AntonisPsarras/guardian-system/scripts.yaml

guardian_set_display:
  alias: Guardian - Set Portal Display
  description: >-
    The single way to put a verdict on the portal. Writes the state string and
    then bumps input_number.portal_display_seq.

    The bump is the whole point. input_text.set_value writing a value the helper
    ALREADY holds emits no state_changed event, and two consumers depended on
    that event: "Guardian: Portal LED Mirror", whose GRANTED branch sleeps three
    seconds and then writes IDLE, and the portal's own repaint/backlight wake,
    which tested "st != ui_prev_state".

    So a second identical verdict arriving inside the first one's three-second
    window was swallowed entirely - the screen never acknowledged it, and the
    FIRST run's delay still dropped the screen to IDLE underneath it. Scanning a
    card immediately after enrolling it is exactly that sequence (enrollment
    writes GRANTED, the scan writes GRANTED again), which is why a freshly
    enrolled card appeared to be ignored while its welcome tone and green lamp
    still fired. Unknown cards write a DIFFERENT value, DENIED_CARD, so they
    always changed state and always rendered - the asymmetry that made this look
    like a card-matching bug.

    A counter that always changes makes every verdict observable, repeat or not.
  # queued: this is a read-modify-write on the counter and several automations
  # can call it at once. Queued runs execute sequentially, and action data
  # templates render per-run at execution time, so the increment cannot lose a
  # write the way an automation-level variable would.
  #
  # max is 25 rather than 10 because ONE caller must never be dropped. A
  # blocking "action: script.guardian_set_display" against a queued script that
  # is already at max is DISCARDED with a log warning - it does not raise, and
  # the caller carries on as if it had run. In "Guardian: Major Alarm Handler"
  # that call is the one deliberately unguarded step, on the reasoning that a
  # failure there means the siren cannot run anyway; the siren loop's
  # while-condition reads the state this script writes. So a dropped run there
  # is an alarm that pushes, returns cleanly, and produces NO siren, NO ALARM
  # screen and no error anywhere - the queue depth is the only thing standing
  # between that and a burst of display writes from a keypad, an enrollment and
  # a scan arriving together. Runs are two helper writes and finish in
  # milliseconds; the depth costs nothing and is not a substitute for keeping
  # this script cheap.
  mode: queued
  max: 25
  fields:
    value:
      description: Display state string, e.g. GRANTED, DENIED_CARD, CHALLENGE, IDLE
      required: true
  sequence:
  - action: input_text.set_value
    target:
      entity_id: input_text.portal_display_state
    data:
      value: '{{ value }}'
  # THE ALARM'S ONLY MEMORY ACROSS A RESTART, and it is written here rather than
  # at any of the fifty-odd call sites deliberately.
  #
  # portal_display_state is declared initial: none, which Home Assistant applies
  # on every start and which skips restore_state - so the display cannot carry an
  # alarm across a restart, and "Guardian: Startup State Recovery" spent its whole
  # life testing it for ALARM in a branch that could never be true. A restart
  # ended a live alarm in total silence: no siren, no second push, and the code
  # written to resume it was unreachable.
  #
  # This script's own alias is "the single way to put a verdict on the portal",
  # and that is exactly the property the latch needs. Setting it here means the
  # latch and the screen move together or not at all - every existing writer,
  # including "Guardian: Dismiss Alarm from Phone" and guardian_reset, clears the
  # latch correctly with no edit, and a future one cannot forget to. Writing it
  # from the call sites instead would be fifty chances to disagree with the
  # screen about whether the house is alarming.
  #
  # GUARDED, AND IT MATTERS WHICH SIDE OF THE DISPLAY WRITE IT SITS ON.
  #
  # The write above is the one deliberately unguarded step in the alarm path,
  # because the siren loop's while-condition reads what it writes: if that fails
  # the siren genuinely cannot run and the error belongs in the log. THIS step
  # does not have that property. Failing to record the latch means an alarm will
  # not survive a restart, which is strictly less bad than an alarm that never
  # sounds - so it must not be able to take the sounding one with it.
  #
  # And it would have been able to. guardian_set_display is called BLOCKING from
  # "Guardian: Major Alarm Handler", so a step that ends this script ends the
  # handler too - in front of its own siren loop. That is the exact fault the
  # fortieth and forty-second passes each fixed once: a cosmetic step standing in
  # front of the siren, with a comment above it explaining why it was safe. On a
  # half-installed tree - packages/guardian.yaml not copied, or copied and only
  # reloaded rather than fully restarted - this helper does not exist, and that
  # is precisely the case the alarm path has already been found failing in.
  #
  # The entity_id is a literal constant, so it cannot fail the service schema and
  # the one failure mode left is a missing or unavailable entity, which is what
  # continue_on_error genuinely does catch.
  - action: input_text.set_value
    continue_on_error: true
    target:
      entity_id: input_text.guardian_alarm_latch
    data:
      # A timestamp, not a flag: the startup reader needs to know HOW LONG AGO,
      # because a restore snapshot can be fifteen minutes stale and an alarm that
      # started eight hours ago is a power cut, not an intrusion.
      value: "{{ now().isoformat() if value == 'ALARM' else 'none' }}"
  - action: input_number.set_value
    target:
      entity_id: input_number.portal_display_seq
    data:
      value: "{{ (states('input_number.portal_display_seq') | int(0) + 1) % 10000 }}"

process_rfid_scan:
  alias: Guardian - Process RFID Scan
  description: >-
    Validates one scan and starts an entry, exit, or MFA passage window.

    NOTHING in here may block. Every lamp call is fired with script.turn_on
    rather than "action: script.guardian_lamp_*", because "action:" WAITS for the
    called script to finish and guardian_lamp_feedback takes 2-3 seconds on a
    good day: a 15s wait_template on the sampling flag, a light.turn_on against a
    cloud-connected Tapo bulb, a 1s hold, then a restore.

    That is how this script silently stopped seeing cards. It is queued with
    max: 10, so ten runs each parked on the lamp fill the queue and Home
    Assistant DROPS every further scan with only a warning in the log - no
    screen change, no audio, nothing on the ESP. It went unnoticed while
    enrollment disabled itself after a single card; now that a session stays
    open and cards are presented one after another, the queue fills in seconds
    and the reader appears to go dead.

    The remaining "action: script.*" calls are guardian_set_display,
    guardian_reconcile_presence, guardian_authorize_passage and
    guardian_clear_entry_challenge. All of them are helper writes and events;
    none wait on the lamp or a delay. They stay as "action:" because the
    branch after them depends on their result. Do not convert them to
    script.turn_on, and do not put a delay or a lamp wait back in this script.
  mode: queued
  max: 10
  fields:
    uid:
      description: Legacy factory UID from pre-authenticator firmware. Ignored when result is set.
      required: false
    source:
      description: doorbell or interior_portal
      required: true
    result:
      description: ok, enrolled, write_fail, bad_mac, or unsupported_tag
      required: false
    card_id:
      description: 16-character hex card_id from the on-card authenticator
      required: false
    counter:
      description: Counter reported by the reader (post-rotate when rotated is true)
      required: false
    rotated:
      description: true if the reader wrote the next counter to the card
      required: false
    protected:
      description: >-
        "true" or "false" from the reader: whether this tag's payload is
        password-protected on the card. EMPTY MEANS UNKNOWN, not false - a
        reader running firmware older than the forty-third pass does not send
        this field at all, and every device in this house is currently running
        such a build. Recorded only; it gates nothing.
      required: false
  sequence:
  - variables:
      scan_result: '{{ result | default('''', true) | string | trim | lower }}'
      card_id_norm: '{{ card_id | default('''', true) | string | trim | lower }}'
      counter_n: '{{ counter | default(0, true) | int(0) }}'
      rotated_b: '{{ (rotated | default(false, true) | string | lower) in [''true'', ''on'', ''1''] }}'
      uid_raw: '{{ uid | default('''', true) | string | trim }}'
      uid_hash: '{{ uid | default('''', true) | string | trim | sha256 if (uid | default('''', true) | string | trim | length) > 0 else '''' }}'
      slot_ids: "{{ (states('sensor.guardian_rfid_slots') | string).split(',')
                   | map('trim') | reject('eq', '') | list }}"
      # Occupied = 16 hex card_id. A leftover rfid_N_hash is not a credential.
      matched_slot: >-
        {% set ids = (states('sensor.guardian_rfid_slots') | string).split(',')
                     | map('trim') | reject('eq', '') | list %}
        {% set cid = card_id | default('', true) | string | trim | lower %}
        {% set ns = namespace(slot='') %}
        {% if cid | length == 16 and cid is match('^[0-9a-f]{16}$') %}
          {% for i in ids %}
            {% set stored = states('input_text.rfid_' ~ i ~ '_card_id')
                            | string | trim | lower %}
            {% if stored | length == 16 and stored is match('^[0-9a-f]{16}$')
                 and stored == cid %}
              {% set ns.slot = i | string %}
            {% endif %}
          {% endfor %}
        {% elif (result | default('', true) | string | trim | length) == 0 %}
          {# Pre-flash firmware still sends uid and no result. Match the old
             hash for the one-restart overlap, then it dies: enrollment no
             longer writes hashes, and flashed readers always send result. #}
          {% set uh = uid | default('', true) | string | trim | sha256 %}
          {% for i in ids %}
            {% set stored = states('input_text.rfid_' ~ i ~ '_hash')
                            | string | trim | lower %}
            {% if stored | length == 64 and stored == uh %}
              {% set ns.slot = i | string %}
            {% endif %}
          {% endfor %}
        {% endif %}
        {{ ns.slot }}
      empty_slot: >-
        {% set ids = (states('sensor.guardian_rfid_slots') | string).split(',')
                     | map('trim') | reject('eq', '') | list %}
        {% set ns = namespace(slot='') %}
        {% for i in ids %}
          {% set value = states('input_text.rfid_' ~ i ~ '_card_id')
                         | string | trim | lower %}
          {% if ns.slot == '' and not (value | length == 16
               and value is match('^[0-9a-f]{16}$')) %}
            {% set ns.slot = i | string %}
          {% endif %}
        {% endfor %}
        {{ ns.slot }}
      # Single source of truth - see binary_sensor.guardian_elevated_mode in
      # packages/guardian.yaml. This used to read
      # "super_surveillance_mode == on or now().hour < 5" inline, one of four
      # copies, which meant the clock half could not be switched off and no
      # automation anywhere could react to elevated mode ending. Elevated is
      # now the manual boolean OR the Super Surveillance schedule.
      elevated_mode: "{{ is_state('binary_sensor.guardian_elevated_mode', 'on') }}"
      enroll_mode: "{{ is_state('input_boolean.guardian_enrollment_mode', 'on') }}"
      enroll_as_visitor: "{{ is_state('input_boolean.guardian_enroll_as_visitor', 'on') }}"
      # A grace challenge is open: the door was opened in elevated mode without a
      # completed passage window, and someone has a few seconds to present BOTH
      # a registered card and the master PIN. One factor is not enough.
      challenge_active: "{{ is_state('input_boolean.guardian_entry_challenge', 'on') }}"
      # Which slot an enrollment writes to. The keypad choice wins; otherwise the
      # first free slot; empty when every slot is occupied and nothing was
      # chosen, which is now an explicit "pick a slot" prompt on the portal
      # rather than a silent refusal.
      #
      # sensor.guardian_enrollment_target_slot computes exactly this and is what
      # the portal renders, but it is deliberately NOT read here: a template
      # sensor is recomputed from a state change, and enrolling two cards back to
      # back would race it - the second card could be written into the slot the
      # first one just took. This is derived from the helpers directly so the
      # write is always against current truth.
      target_slot: >-
        {%- set ids = (states('sensor.guardian_rfid_slots') | string).split(',')
                      | map('trim') | reject('eq', '') | list -%}
        {%- set chosen = states('input_text.guardian_enrollment_slot')
                         | string | trim -%}
        {{- chosen if chosen in ids else (empty_slot | string | trim) -}}
      # Home Assistant coerces a script variable whose rendered value is only
      # digits into an int. empty_slot / target_slot / matched_slot therefore
      # arrive at the choose as 1, not "1". Jinja's `1 in ['1','2']` is
      # false, so enrollment with empty hashes took ENROLL_PICK ("no
      # target slot") while the trace printed target_slot: '1'. Every
      # comparison below must `| string | trim` before testing membership.
      slot_ok: "{{ (matched_slot | string | trim) in ((states('sensor.guardian_rfid_slots')
        | string).split(',') | map('trim') | reject('eq', '') | list) }}"
      target_ok: "{{ (target_slot | string | trim) in ((states('sensor.guardian_rfid_slots')
        | string).split(',') | map('trim') | reject('eq', '') | list) }}"
      # Freshness window against the last counter Home Assistant stored.
      # seen is the counter that was on the card BEFORE a successful rotate.
      # Accept stored-1 (last write did not stick) and anything newer (HA missed
      # a rotate, or the other reader already wrote). Older than stored-1 is a
      # dump clone. The old stored+1 cap treated a double-scan the reader
      # ingested once as CLONE; that high cap is not clone detection.
      #
      # The `not (rot and reported <= stored)` clause is REPLAY protection, and
      # it is deliberately narrow. esphome.rfid_scanned is an ordinary event on
      # the bus: any account that can authenticate to Home Assistant can POST one
      # to /api/events/esphome.rfid_scanned, and the two values needed to build a
      # convincing payload - input_text.rfid_N_card_id and
      # input_number.rfid_N_counter - are readable from the states API. The
      # firmware's HMAC is not checked here; only this window is.
      #
      # Work out which case actually changes. For a rotated scan the old rule
      # reduces to `stored <= reported` (substitute seen = reported - 1). The new
      # clause requires `stored < reported`. So the ONLY behaviour that changes is
      # rotated scans where reported == stored exactly - a card claiming to have
      # just rotated INTO a value Home Assistant has already recorded. A genuine
      # tap can never do that: the write-back below stores `reported`, so the next
      # genuine tap of the same card reports stored + 1. Replaying a captured
      # event verbatim is precisely the case that produces reported == stored.
      #
      # Non-rotated scans (rot false, the card write failed) are untouched, and
      # so is the stale-dump case, which the lower bound already caught.
      #
      # The cost of a false positive here is not small - this branch produces the
      # CLONE verdict, a critical push, and a major alarm if a challenge is open -
      # so if a real double-tap ever reports CLONE, this clause is the first thing
      # to look at, not the branch ordering further down.
      window_ok: >-
        {% set slot = matched_slot | string | trim %}
        {% set ids = (states('sensor.guardian_rfid_slots') | string).split(',')
                     | map('trim') | reject('eq', '') | list %}
        {% if slot not in ids %}
          {{ false }}
        {% else %}
          {% set stored = states('input_number.rfid_' ~ slot ~ '_counter') | int(0) %}
          {% set reported = counter | default(0, true) | int(0) %}
          {% set rot = (rotated | default(false, true) | string | lower)
                       in ['true', 'on', '1'] %}
          {% set seen = reported - (1 if rot and reported > 0 else 0) %}
          {{ (stored - 1 <= seen) and not (rot and reported <= stored) }}
        {% endif %}
      tag_unsupported: "{{ scan_result == 'unsupported_tag' }}"
      enroll_hold: "{{ scan_result in ['write_fail', 'bad_mac'] }}"
      # THREE-VALUED ON PURPOSE: 'true', 'false', or '' for not-stated. Anything
      # the reader did not send stays '' and is recorded as nothing at all,
      # because a firmware that predates this field is indistinguishable from one
      # reporting an unprotected tag if the two are collapsed - and the whole
      # point of surfacing this is to tell a household which of their keys are
      # clonable. Reading silence as "unprotected" would accuse every key in the
      # house; reading it as "protected" would clear them all. It reads as
      # neither.
      protected_norm: >-
        {% set p = protected | default('', true) | string | trim | lower %}
        {{ 'true' if p in ['true', 'on', '1', 'yes']
           else ('false' if p in ['false', 'off', '0', 'no'] else '') }}
  # A key flagged Stolen/Lost, presented at EITHER reader, sounds the alarm here
  # and now - before the decision trace, before reconcile, before the counter
  # write, before the choose. Both readers reach this line: the doorbell and the
  # portal both dispatch through "Guardian: RFID Scanned" into this one script,
  # and both are heard on the portal's DFPlayer, which is where every other
  # scan sound already comes from.
  #
  # The assumption is that the person holding a key its owner reported missing
  # is an intruder standing at the door right now, so this must not wait on
  # anything that can be slow or absent. It reads two local helpers and presses
  # one ESPHome button on the LAN: no phone link, no cloud bulb, no broadcast.
  # This press, and ONLY this press, is what has to happen with no latency. It
  # is not routed through guardian.major_alarm because that handler writes the
  # reason, sets the display and fires notify_broadcast before it reaches its
  # play loop. The alarm proper is raised a few lines below, once matched_name
  # exists; that is what sustains the siren, lights the screen and offers the
  # phone its Disable Alarm button. This is just the first note of it, early.
  #
  # Nothing above it may suppress it either. There is no cooldown or
  # "already alarming" test here on purpose: a second stolen tap means someone
  # is still at the door, and a silent second tap is the failure this exists to
  # prevent.
  #
  # continue_on_error, and it is the whole difference between an early note and
  # a silent alarm. The press targets an entity on the PORTAL; the scan can come
  # from the DOORBELL, which does not need the portal to be up. With the portal
  # unavailable - rebooting, roaming between access points, the five minutes
  # "Guardian: Portal Offline Watchdog" exists to announce - button.press raises,
  # and a raising step ends the sequence. Unguarded, this line took the whole
  # script down with it: guardian.major_alarm below never fired, so there was no
  # push, no reason written, no ALARM display and no siren loop to resume when
  # the portal came back, and the rest of process_rfid_scan - trace, reconcile,
  # counter write, the entire choose - never ran either. A stolen key at the
  # door produced silence.
  #
  # This is the same class of fault the Major Alarm Handler was fixed for in
  # 8e89db4, on a worse path: it needs no half-copied install and no startup
  # race, only a portal that is briefly off the network. The guard costs
  # nothing - continue_on_error adds no latency and does not defer the press,
  # it only stops a failed press from suppressing everything after it. If the
  # speaker cannot sound, the alarm proper below still must.
  - if:
    - condition: template
      value_template: "{{ slot_ok | bool and
        states('input_select.rfid_' ~ (matched_slot | string | trim))
          in ['Stolen', 'Stolen/Lost'] }}"
    then:
    - action: button.press
      continue_on_error: true
      target:
        entity_id: button.guardian_interior_portal_play_alarm
  - variables:
      # Person name for user-facing copy. Recomputed here so it can read
      # matched_slot from the previous variables block (same-block keys cannot
      # reference each other).
      matched_name: >-
        {% set i = matched_slot | string | trim %}
        {% set raw = states('input_text.rfid_' ~ i ~ '_name') | string | trim %}
        {{ raw if raw not in ['', 'unknown', 'unavailable']
           else ('Key ' ~ i if i else '') }}
      # Presence BEFORE reconcile. A doorbell scan of an "At home" card is an
      # exit that already left the house; reconcile would flip it to Away and
      # hide that from every later branch. Capture it here, then never read
      # input_select.rfid_N again for this decision.
      presence_before: >-
        {% set i = matched_slot | string | trim %}
        {{ states('input_select.rfid_' ~ i) | string | trim }}
      door_closed: "{{ is_state('binary_sensor.guardian_interior_portal_door_contact', 'off') }}"
      # Exterior reader, door shut, elevated: the keypad is unreachable. Either
      # a live 30s challenge (they just walked out) or presence still At home
      # (they left without scanning inside) is an exit that needs the 10-minute
      # phone PIN, not MFA at a keypad they cannot reach.
      doorbell_exit: "{{ (elevated_mode | bool) and (source == 'doorbell')
        and (door_closed | bool) and (slot_ok | bool)
        and ((challenge_active | bool) or (presence_before == 'At home')) }}"
  # Raise the alarm proper for a Stolen/Lost key, still ahead of the trace,
  # reconcile, the counter write and the choose. The siren already started
  # above; this is what keeps it going and makes it stoppable.
  #
  # Everything the previous version of this had to invent, the major alarm
  # already owns, which is why it is now raised unconditionally here rather
  # than only when a challenge happened to be live:
  #
  #   * the siren repeats on a 3s cadence for as long as the display says
  #     ALARM, instead of a fixed count that ran out while the intruder was
  #     still at the door;
  #   * "Guardian: Dismiss Alarm from Phone" answers MUTE_GUARDIAN_ALARM by
  #     writing IDLE, which is what ends that loop - the phone button the
  #     super surveillance alarm already offers now stops this one too;
  #   * the portal paints its full-screen ALARM with the reason below. The
  #     STOLEN screen could not be used for this: "Guardian: Portal LED Mirror"
  #     drops STOLEN back to IDLE after three seconds, so the screen went blank
  #     while the siren kept sounding.
  #
  # The reason is rendered at 35 characters on a 240px panel, so it leads with
  # the two words that matter and abbreviates the reader rather than letting a
  # long name push them off the end.
  - if:
    - condition: template
      value_template: "{{ slot_ok | bool and
        states('input_select.rfid_' ~ (matched_slot | string | trim))
          in ['Stolen', 'Stolen/Lost'] }}"
    then:
    - event: guardian.major_alarm
      event_data:
        reason: >-
          Stolen key: {{ matched_name if matched_name else 'Key ' ~
          (matched_slot | string | trim) }} at {{ 'door' if source == 'doorbell'
          else 'portal' }}
  # Decision trace. OFF unless input_boolean.guardian_verbose_notifications is on.
  #
  # This lives HERE, inside the script, rather than in an automation watching the
  # event, because it has to report the variables the choose below will actually
  # branch on. Every other vantage point - the device log, the event bus, a
  # template sensor - shows an input to this decision rather than the decision,
  # and the failures being chased have all been cases where the inputs looked
  # right and the outcome was still wrong.
  #
  # It names the branch outright, computed from the same conditions in the same
  # order, so "which branch ran" stops being an inference from an LED colour.
  - if:
    - condition: state
      entity_id: input_boolean.guardian_verbose_notifications
      state: 'on'
    then:
    # continue_on_error: this is a diagnostic, and it sits in front of every
    # alert the scan can raise - the stolen-key alarm, the clone push and the
    # clone alarm all come after it. A trace that can cancel the thing it exists
    # to explain is worse than no trace.
    - action: persistent_notification.create
      continue_on_error: true
      data:
        notification_id: "guardian_scan_trace_{{ now().strftime('%H%M%S') }}"
        title: >-
          {{ now().strftime('%H:%M:%S') }} {{ source }} ->
          {%- set m = matched_slot | string | trim -%}
          {%- set valid = slot_ok | bool -%}
          {% if valid and states('input_select.rfid_' ~ m)
                in ['Stolen', 'Stolen/Lost'] %} STOLEN
          {%- elif doorbell_exit | bool %} DOORBELL EXIT PIN
          {%- elif challenge_active | bool and valid %} CHALLENGE CARD
          {%- elif enroll_mode | bool and valid %} ENROLL_DUP
          {%- elif valid and not (window_ok | bool) and scan_result not in ['', 'enrolled'] %} CLONE
          {%- elif enroll_hold | bool %} HOLD
          {%- elif valid and elevated_mode | bool %} MFA
          {%- elif valid %} GRANTED (passage)
          {%- elif enroll_mode | bool and tag_unsupported | bool %} UNSUPPORTED
          {%- elif enroll_mode | bool and enroll_hold | bool %} HOLD
          {%- elif enroll_mode | bool and target_ok | bool %} ENROLL -> slot {{ target_slot | string | trim }}
          {%- elif enroll_mode | bool %} ENROLL_PICK (no target slot)
          {%- elif tag_unsupported | bool %} UNSUPPORTED
          {%- else %} DENIED_CARD{% endif %}
        message: >-
          result: {{ scan_result }}
          · card_id_len: {{ card_id_norm | length }}
          · counter: {{ counter_n }}
          · rotated: {{ rotated_b }}
          · window: {{ window_ok }}

          matched_slot: '{{ matched_slot | string | trim }}'
          · empty_slot: '{{ empty_slot | trim }}'
          · target_slot: '{{ target_slot | string | trim }}'

          enroll_mode: {{ enroll_mode }}
          · guest: {{ enroll_as_visitor }}
          · elevated: {{ elevated_mode }}
          · challenge: {{ challenge_active }}
          · doorbell_exit: {{ doorbell_exit }}
          · presence_before: '{{ presence_before }}'

          enrollment_slot helper: '{{ states('input_text.guardian_enrollment_slot') }}'

          stored: {% set ids = (states('sensor.guardian_rfid_slots') | string).split(',')
                               | map('trim') | reject('eq', '') | list %}{% for i in ids %}{{ i }}={{
            states('input_text.rfid_' ~ i ~ '_card_id') | string | trim | lower | length }}ch/c{{
            states('input_number.rfid_' ~ i ~ '_counter') | int(0) }} {% endfor %}
  # Self-correction, before any branch. The reader a card was presented to tells
  # us which side of the door that card is physically on, so a card recorded as
  # "Away" and scanned on the interior portal - or "At home" and scanned at the
  # doorbell - is provably out of date from an earlier missed scan. Fix it now
  # rather than letting the error persist.
  #
  # Placed ahead of the choose so it covers the normal path AND the elevated
  # MFA path from one call site. Stolen cards are excluded: their branch is a
  # security response, and their input_select state must not be touched.
  - if:
    - condition: template
      value_template: "{{ slot_ok | bool and
        (scan_result == '' or window_ok | bool) and
        states('input_select.rfid_' ~ (matched_slot | string | trim))
          not in ['Stolen', 'Stolen/Lost'] }}"
    then:
    - action: script.guardian_reconcile_presence
      data:
        slot: '{{ matched_slot | string | trim }}'
        source: '{{ source }}'
  # Record the new counter only after the window accepted it, and only when the
  # reader actually wrote. A failed rotate leaves HA where it was so the next
  # tap still matches. A clone (window fail) must not advance this.
  - if:
    - condition: template
      value_template: "{{ slot_ok | bool and rotated_b | bool and
        (scan_result == '' or window_ok | bool) }}"
    then:
    - action: input_number.set_value
      continue_on_error: true
      target:
        entity_id: input_number.rfid_{{ matched_slot | string | trim }}_counter
      data:
        value: "{{ [states('input_number.rfid_' ~ (matched_slot | string | trim) ~ '_counter')
          | int(0), counter_n | int(0)] | max }}"
  # Read back before any grant. continue_on_error above means a missing helper
  # cannot abort the stolen-key path that already ran, but it also used to
  # swallow a persist that never landed - then GRANTED still fired, and the
  # next tap looked like a replay. Fail closed: if this rotate did not stick
  # on the helper, no passage window.
  - variables:
      counter_ok: "{{ (not (slot_ok | bool) or not (rotated_b | bool)) or
        (states('input_number.rfid_' ~ (matched_slot | string | trim) ~ '_counter')
         | int(0) >= (counter_n | int(0))) }}"
  # WHETHER THIS KEY IS PASSWORD-PROTECTED ON THE CARD. Recorded here, shown in
  # the panel's key list, and USED FOR NOTHING ELSE.
  #
  # The reader has published this on every scan since the forty-third pass and
  # nothing has ever read it - the field went onto the event bus and stopped
  # there, while DEPLOY.md recorded it as "surfaced to the household". An
  # unprotected NTAG's payload can be read by any reader, and a readable bearer
  # token is a clonable card, so the household has a reason to know which of
  # their keys are in that state.
  #
  # IT MUST NEVER GATE ACCESS, and that is not caution, it is the two lessons
  # this component has already paid for: refusing an unprotected tag would lock
  # out every card enrolled before the protection fix existed, which is the
  # entire house, and it is the population that most needs to be let in and told.
  # This step writes one CSV helper. It is not read by any condition on any path
  # that opens a door.
  #
  # Only writes on a definite verdict. protected_norm is '' when the reader did
  # not state it, and a slot is then left exactly as it was rather than being
  # cleared - a scan from an old firmware must not erase a finding a new one made.
  - if:
    - condition: template
      value_template: "{{ slot_ok | bool and protected_norm in ['true', 'false'] }}"
    then:
    - action: input_text.set_value
      continue_on_error: true
      target:
        entity_id: input_text.guardian_card_protection
      data:
        # Rebuilt from the current value on every write rather than appended to,
        # so the string cannot accumulate duplicate or stale entries. Entries for
        # slots that no longer exist are dropped, this slot's old entry is
        # replaced by the fresh verdict, and the result is sorted so two
        # identical sets are always the same string - a helper that flickers
        # between equivalent orderings would repaint the panel for no reason.
        value: >-
          {%- set slot = matched_slot | string | trim -%}
          {%- set ids = (states('sensor.guardian_rfid_slots') | string).split(',')
                        | map('trim') | reject('eq', '') | list -%}
          {%- set held = (states('input_text.guardian_card_protection') | string)
                         .split(',') | map('trim') | reject('eq', '') | list -%}
          {%- set ns = namespace(out=[]) -%}
          {%- for e in held -%}
            {%- if e is match('^[0-9]+[pu]$') -%}
              {%- set who = e[:-1] -%}
              {%- if who != slot and who in ids -%}
                {%- set ns.out = ns.out + [e] -%}
              {%- endif -%}
            {%- endif -%}
          {%- endfor -%}
          {%- set ns.out = ns.out
                + [slot ~ ('u' if protected_norm == 'false' else 'p')] -%}
          {{- ns.out | sort | join(',') -}}
  - choose:
    - conditions:
      - condition: template
        value_template: '{{ tag_unsupported | bool }}'
      sequence:
      - event: guardian.unknown_card_scanned
        event_data:
          source: '{{ source }}'
          result: unsupported_tag
      - action: script.guardian_set_display
        data:
          value: UNSUPPORTED
      - action: button.press
        target:
          entity_id: button.guardian_interior_portal_play_denied
      - action: script.turn_on
        target:
          entity_id: script.guardian_lamp_rejected
    - conditions:
      - condition: template
        value_template: '{{ slot_ok | bool and scan_result not in ['''', ''enrolled'']
          and not (window_ok | bool) and states(''input_select.rfid_'' ~
          (matched_slot | string | trim)) not in [''Stolen'', ''Stolen/Lost''] }}'
      sequence:
      - event: guardian.clone_card_scanned
        event_data:
          slot: '{{ matched_slot | string | trim }}'
          name: '{{ matched_name }}'
          source: '{{ source }}'
          counter: '{{ counter_n }}'
      - action: script.guardian_notify_person
        continue_on_error: true
        data:
          slot: '{{ matched_slot | string | trim }}'
          critical: true
          category: security
          severity: urgent
          title: 'Guardian: copied key rejected'
          message: >-
            {{ matched_name if matched_name else 'Key ' ~ (matched_slot | string | trim) }}
            presented a stale counter at the {{ source }} reader. The real key
            still works; this copy does not. Flag Stolen/Lost if the original
            is missing.
      - action: script.guardian_set_display
        data:
          value: CLONE
      # Guarded for the same reason as the stolen-key press above: this targets
      # a PORTAL entity and a clone can be presented at the doorbell, so an
      # offline portal made this raise and end the branch - taking the
      # guardian.major_alarm below with it. guardian_set_display above stays
      # unguarded on the Major Alarm Handler's rule: the display state is what
      # the siren loop repeats on, so a failure there means no siren regardless
      # and the error belongs in the log rather than swallowed.
      - action: button.press
        continue_on_error: true
        target:
          entity_id: button.guardian_interior_portal_play_denied
      - action: script.turn_on
        target:
          entity_id: script.guardian_lamp_rejected
      # Same escalation as the stolen branch below, for the same reason. This
      # branch is evaluated BEFORE the challenge-factor branch and wins, so a
      # forged copy presented to answer a live challenge used to produce CLONE
      # on the display, a critical push and a red flash - and then nothing, until
      # the challenge ran out 30 seconds later and alarmed with the generic "not
      # authenticated" reason. A copy of a card that is still in its owner's
      # pocket is at least as strong an intruder signal as one already reported
      # missing, and the person holding it is standing at the door now. Do not
      # reorder the branches to "fix" this instead - the clone verdict has to win
      # so the display and the counter logic stay correct.
      - if:
        - condition: template
          value_template: '{{ challenge_active | bool }}'
        then:
        - event: guardian.major_alarm
          event_data:
            reason: >-
              Cloned key ({{ (matched_name ~ ', ') if matched_name else '' }}slot
              {{ matched_slot | string | trim }}) presented to answer an
              elevated-mode entry challenge
    - conditions:
      - condition: template
        value_template: '{{ enroll_mode | bool and not (slot_ok | bool)
          and enroll_hold | bool }}'
      sequence:
      - action: script.guardian_set_display
        data:
          value: HOLD
      - action: button.press
        target:
          entity_id: button.guardian_interior_portal_play_denied
      - action: timer.start
        target:
          entity_id: timer.guardian_enrollment_window
    - conditions:
      - condition: template
        value_template: '{{ slot_ok | bool }}'
      - condition: template
        value_template: '{{ states(''input_select.rfid_'' ~ (matched_slot | string | trim))
          in [''Stolen'', ''Stolen/Lost''] }}'
      sequence:
      - event: guardian.stolen_card_scanned
        event_data:
          slot: '{{ matched_slot | string | trim }}'
          name: '{{ matched_name }}'
          source: '{{ source }}'
      # This branch now announces the scan and nothing else. The major alarm
      # raised at the top of the script owns the screen, the lamp and the
      # speaker for the rest of this event, and each of the three things that
      # used to be done here actively fought it:
      #
      #   * set_display STOLEN raced the handler's own write of ALARM. Landing
      #     second, it took the screen off ALARM - which is the exact condition
      #     the siren loop repeats on - and silenced the alarm about a second
      #     after it started.
      #   * play_denied replaced the alarm track on the DFPlayer, which plays
      #     one file at a time, so a stolen key sounded like an unknown one.
      #   * lamp_rejected flashed red three times and ended on light.turn_off,
      #     then hit its own "Alarm owns the lamp" stop before restoring
      #     anything - leaving the bulb DARK for the rest of an alarm the
      #     handler had just pinned solid red.
      #
      # The escalation that used to be conditional on challenge_active is gone
      # for the same reason: the alarm is now raised for every stolen scan,
      # which is what a key its owner reported missing warrants regardless of
      # whether a challenge happened to be open.
    - conditions:
      - condition: template
        value_template: '{{ slot_ok | bool and rotated_b | bool
          and not (counter_ok | bool) }}'
      sequence:
      # The card write was reported, but input_number.rfid_N_counter did not
      # take the new value. Granting here would play welcome and open a
      # passage window while HA still holds the old counter - or, if a later
      # retry then persisted, the next genuine tap would look like a replay.
      - action: persistent_notification.create
        continue_on_error: true
        data:
          notification_id: guardian_rfid_counter_write_failed
          title: 'Guardian: key counter did not save'
          message: >-
            Slot {{ matched_slot | string | trim }} reported counter
            {{ counter_n | int(0) }} from the {{ source }} reader, but
            input_number.rfid_{{ matched_slot | string | trim }}_counter
            still reads
            {{ states('input_number.rfid_' ~ (matched_slot | string | trim)
               ~ '_counter') | int(0) }}. Passage was not granted.
            Re-present the key after the helper is writable. Hold still and
            retry; do not re-enroll unless the same key has been HOLDed three
            times in a row. Re-enrolling mints a new card_id and hides a
            counter that did not stick.
      - action: script.guardian_set_display
        data:
          value: HOLD
      - action: button.press
        continue_on_error: true
        target:
          entity_id: button.guardian_interior_portal_play_denied
    - conditions:
      - condition: template
        value_template: '{{ enroll_hold | bool and slot_ok | bool }}'
      sequence:
      # Matched write_fail / bad_mac used to fall through to authorize_passage
      # and play welcome. Firmware now retries silently while the tag is on
      # the coil and only emits write_fail when it leaves still failing, so
      # this is the terminal outcome: keep the card, do not open a door.
      # Re-enroll is not the first remedy: it mints a new card_id and resets
      # the counter, which masks a torn rotate. Hold and retry; re-enroll only
      # after three HOLDs on this same key.
      - action: persistent_notification.create
        continue_on_error: true
        data:
          notification_id: guardian_rfid_hold_retry
          title: 'Guardian: hold the key and retry'
          message: >-
            Slot {{ matched_slot | string | trim }} at the {{ source }} reader
            reported {{ scan_result }} (counter
            {{ counter_n | int(0) }}, rotated {{ rotated_b }}). Passage was
            not granted. Keep the key on the reader and tap again. Do not
            re-enroll unless this same key has been HOLDed three times in a
            row — re-enrolling hides a torn write instead of healing it.
      - action: script.guardian_set_display
        data:
          value: HOLD
      - action: button.press
        continue_on_error: true
        target:
          entity_id: button.guardian_interior_portal_play_denied
    # A registered card is one factor of a grace challenge, never both. The
    # previous either/or (card alone cleared it) is the loophole this branch
    # exists to close. Doorbell-exit (door shut, keypad unreachable) is handled
    # above so it is not forced through a 30s keypad wait the owner cannot
    # answer.
    - conditions:
      - condition: template
        value_template: '{{ doorbell_exit | bool }}'
      - condition: template
        value_template: '{{ slot_ok | bool }}'
      sequence:
      - action: script.guardian_start_doorbell_exit_pin
        data:
          slot: '{{ matched_slot | string | trim }}'
          convert_challenge: '{{ challenge_active | bool }}'
    - conditions:
      - condition: template
        value_template: '{{ challenge_active | bool }}'
      - condition: template
        value_template: '{{ slot_ok | bool }}'
      sequence:
      - action: input_boolean.turn_on
        target:
          entity_id: input_boolean.guardian_challenge_card_ok
      - action: input_text.set_value
        target:
          entity_id: input_text.pending_mfa_slot
        data:
          value: '{{ matched_slot | string | trim }}'
      - action: input_text.set_value
        target:
          entity_id: input_text.pending_mfa_source
        data:
          value: '{{ source }}'
      - choose:
        - conditions:
          - condition: state
            entity_id: input_boolean.guardian_challenge_pin_ok
            state: 'on'
          sequence:
          - action: script.guardian_clear_entry_challenge
            data:
              method: card
              slot: '{{ matched_slot | string | trim }}'
              detail: >-
                {{ matched_name if matched_name
                   else 'Key ' ~ (matched_slot | string | trim) }} at {{ source }}
                (PIN already entered)
          - action: script.guardian_set_display
            data:
              value: GRANTED
          - action: button.press
            target:
              entity_id: button.guardian_interior_portal_play_welcome
          - action: script.turn_on
            target:
              entity_id: script.guardian_lamp_success
        default:
        # Card is in; PIN is not. Do not restart the 30s clock (a second scan
        # must not extend the window) and do not GRANTED. The green flash is
        # how the scan is acknowledged while the amber hold stays up.
        - action: script.guardian_set_display
          data:
            value: MFA
        - action: script.turn_on
          target:
            entity_id: script.guardian_lamp_success
        - action: button.press
          target:
            entity_id: button.guardian_interior_portal_play_mfa_challenge
        - action: script.guardian_notify_person
          continue_on_error: true
          data:
            slot: '{{ matched_slot | string | trim }}'
            critical: false
            # The flagship "my key" event, and the single biggest source of the
            # noise this feature exists to cut: one push every time you come
            # home. routine, so it stops at Important - but the mine toggle,
            # which is on by default, deliberately lets it through the level
            # floor anyway. That is what "tell me when my card is scanned"
            # means, and the switch that says so is the way to turn it off.
            category: mine
            severity: routine
            title: 'Guardian: card accepted'
            message: >-
              {{ matched_name if matched_name else ('Key ' ~
              (matched_slot | string | trim)) }} was scanned. Super
              surveillance is still on — enter the master PIN at the keypad.
    # Enrollment mode with a card that is ALREADY registered. Without this the
    # tap fell through to the normal matched branch and silently opened a 20s
    # passage window, so the obvious way to check "did that card actually save?"
    # gave no answer to the question being asked.
    - conditions:
      - condition: template
        value_template: '{{ enroll_mode | bool }}'
      - condition: template
        value_template: '{{ slot_ok | bool }}'
      sequence:
      # Applying the session policy here is how an existing card becomes a
      # visitor (or a resident again) without rewriting its hash: enable
      # enrollment, press 0 for guest, tap the card. Stolen cards never reach
      # this branch.
      - variables:
          dup_slot: '{{ matched_slot | string | trim }}'
          desired_policy: "{{ 'visitor' if enroll_as_visitor | bool else 'resident' }}"
          current_policy: "{{ states('input_select.rfid_' ~ (matched_slot | string | trim)
            ~ '_policy') | string | trim }}"
          policy_options: "{{ state_attr('input_select.rfid_' ~ (matched_slot | string | trim)
            ~ '_policy', 'options') | default([], true) | list }}"
          presence_options: "{{ state_attr('input_select.rfid_' ~ (matched_slot | string | trim),
            'options') | default([], true) | list }}"
          dup_pending_name: "{{ states('input_text.guardian_enroll_pending_name')
            | string | trim }}"
      - if:
        - condition: template
          value_template: "{{ desired_policy != current_policy and
            desired_policy in policy_options }}"
        then:
        - action: input_select.select_option
          continue_on_error: true
          target:
            entity_id: input_select.rfid_{{ dup_slot }}_policy
          data:
            option: '{{ desired_policy }}'
        - if:
          - condition: template
            value_template: "{{ desired_policy == 'visitor' and 'Away' in presence_options }}"
          then:
          - action: input_select.select_option
            continue_on_error: true
            target:
              entity_id: input_select.rfid_{{ dup_slot }}
            data:
              option: Away
      # A typed pending name during this session renames the existing key on
      # re-tap (same helper as a fresh enroll). Empty pending leaves the
      # stored name alone. Pending is cleared only after the name sticks.
      - if:
        - condition: template
          value_template: "{{ dup_pending_name not in ['', 'unknown', 'unavailable', 'none'] }}"
        then:
        - action: input_text.set_value
          continue_on_error: true
          target:
            entity_id: input_text.rfid_{{ dup_slot }}_name
          data:
            value: '{{ dup_pending_name }}'
        - variables:
            dup_name_back: "{{ states('input_text.rfid_' ~ dup_slot ~ '_name')
              | string | trim }}"
        - if:
          - condition: template
            value_template: '{{ dup_name_back == dup_pending_name }}'
          then:
          - action: input_text.set_value
            continue_on_error: true
            target:
              entity_id: input_text.guardian_enroll_pending_name
            data:
              value: ''
      # The slot rides along in the state string. The portal reads it as a
      # prefix match, so "which slot is this card already in" is answerable at
      # the door without adding another imported helper for one digit.
      - action: script.guardian_set_display
        data:
          value: 'ENROLL_DUP:{{ matched_slot | string | trim }}'
      - action: button.press
        target:
          entity_id: button.guardian_interior_portal_play_denied
      # Re-presenting a card is how someone confirms an enrollment worked, so it
      # keeps the session alive rather than letting the idle timer run down
      # underneath them.
      - action: timer.start
        target:
          entity_id: timer.guardian_enrollment_window
    - conditions:
      - condition: template
        value_template: '{{ slot_ok | bool }}'
      - condition: template
        value_template: '{{ elevated_mode | bool }}'
      sequence:
      - action: timer.cancel
        target:
          entity_id:
          - timer.guardian_entry_window
          - timer.guardian_exit_window
      - action: input_text.set_value
        target:
          entity_id:
          - input_text.pending_entry_slot
          - input_text.pending_exit_slot
        data:
          value: none
      - action: timer.cancel
        target:
          entity_id: timer.guardian_mfa_window
      - action: input_text.set_value
        target:
          entity_id: input_text.pending_mfa_slot
        data:
          value: '{{ matched_slot | string | trim }}'
      - action: input_text.set_value
        target:
          entity_id: input_text.pending_mfa_source
        data:
          value: '{{ source }}'
      # A challenge starts with a full three attempts. The portal literally
      # promises this - it renders "3 - mfa_failed_attempts" as "N left" - but
      # the counter was only ever zeroed on a correct PIN, on reaching three,
      # and at Home Assistant start. A challenge that ended by timing out, by
      # being superseded, or by the alarm being dismissed left its count
      # standing, so failures accumulated across unrelated sessions until the
      # very first wrong digit of some later challenge tripped the alarm.
      - action: input_number.set_value
        target:
          entity_id: input_number.mfa_failed_attempts
        data:
          value: 0
      - action: input_boolean.turn_on
        target:
          entity_id: input_boolean.portal_mfa_pending
      - action: timer.start
        target:
          entity_id: timer.guardian_mfa_window
      - action: script.guardian_set_display
        data:
          value: MFA
      - action: script.turn_on
        target:
          entity_id: script.guardian_lamp_success
      - action: button.press
        target:
          entity_id: button.guardian_interior_portal_play_mfa_challenge
      - action: script.guardian_notify_person
        continue_on_error: true
        data:
          slot: '{{ matched_slot | string | trim }}'
          critical: false
          category: mine
          severity: routine
          title: 'Guardian: card accepted'
          message: >-
            {{ matched_name if matched_name else ('Key ' ~
            (matched_slot | string | trim)) }} was scanned. Enter the master
            PIN at the keypad to pass.
    - conditions:
      - condition: template
        value_template: '{{ slot_ok | bool }}'
      - condition: template
        value_template: '{{ counter_ok | bool }}'
      - condition: template
        value_template: '{{ scan_result in ['''', ''ok''] }}'
      sequence:
      - action: script.guardian_authorize_passage
        data:
          slot: '{{ matched_slot | string | trim }}'
          source: '{{ source }}'
    - conditions:
      - condition: template
        value_template: '{{ enroll_mode | bool }}'
      - condition: template
        value_template: '{{ target_ok | bool }}'
      - condition: template
        value_template: '{{ not (card_id_norm | length == 16 and card_id_norm is match(''^[0-9a-f]{16}$'')) }}'
      sequence:
      - action: script.guardian_set_display
        data:
          value: HOLD
      - action: button.press
        target:
          entity_id: button.guardian_interior_portal_play_denied
      - action: timer.start
        target:
          entity_id: timer.guardian_enrollment_window
    - conditions:
      - condition: template
        value_template: '{{ enroll_mode | bool }}'
      - condition: template
        value_template: '{{ target_ok | bool }}'
      sequence:
      # Guarded, and not for the usual cosmetic reason: this is the step whose
      # failure the read-back check and the urgent push below EXIST to report.
      # Unguarded, a write that failed outright took both of them down with it
      # and the enrollment failure was reported by nothing at all - the same
      # shape as the fortieth pass's bugs, with the alert reporting on the very
      # step standing in front of it. Let it fail, then let stored_back see that
      # it failed and say so.
      - action: input_text.set_value
        continue_on_error: true
        target:
          entity_id: input_text.rfid_{{ target_slot | string | trim }}_card_id
        data:
          value: '{{ card_id_norm }}'
      - action: input_number.set_value
        continue_on_error: true
        target:
          entity_id: input_number.rfid_{{ target_slot | string | trim }}_counter
        data:
          value: '{{ [counter_n | int(0), 1] | max }}'
      - action: input_text.set_value
        continue_on_error: true
        target:
          entity_id: input_text.rfid_{{ target_slot | string | trim }}_hash
        data:
          value: ''
      - action: input_select.select_option
        continue_on_error: true
        target:
          entity_id: input_select.rfid_{{ target_slot | string | trim }}_policy
        data:
          option: "{{ 'visitor' if enroll_as_visitor | bool else 'resident' }}"
      # continue_on_error, matching the _policy write immediately above, which
      # already had it. input_select.select_option RAISES on an option the helper
      # does not carry - guardian_reconcile_presence says so in its own comment
      # and guards against it with an option_exists test - and a leftover UI
      # helper from before the migration is exactly the disagreement that
      # produces one. Unguarded here it ended the branch in front of the urgent
      # "card did not save" push below. A new card starting on the wrong side of
      # the door is a presence correction away from right; an enrollment failure
      # nobody is told about is not.
      - action: input_select.select_option
        continue_on_error: true
        target:
          entity_id: input_select.rfid_{{ target_slot | string | trim }}
        data:
          # Visitors are never occupants, regardless of which reader enrolled
          # them. Residents still take the reader's side: enrolling at the
          # doorbell means the new card is outside, so hardcoding "At home"
          # started every doorbell-enrolled card on the wrong side of the door.
          option: "{{ 'Away' if enroll_as_visitor | bool else
            ('At home' if source == 'interior_portal' else 'Away') }}"
      # Read the hash back before claiming success.
      #
      # input_text.set_value TRUNCATES silently to the helper's max. These
      # helpers are now declared in packages/guardian_rfid.yaml with max: 64,
      # but a leftover UI helper with a smaller max (the old trap) would still
      # clip. A truncated hash is not 64 characters, so it can never match and
      # is not even counted as occupied: the card enrolls, reports GRANTED, and
      # is then rejected forever. That gets its own unambiguous diagnostic.
      - variables:
          stored_back: "{{ states('input_text.rfid_' ~ (target_slot | string | trim) ~ '_card_id')
            | string | trim | lower }}"
      - if:
        - condition: template
          value_template: '{{ stored_back != card_id_norm }}'
        then:
        - action: persistent_notification.create
          continue_on_error: true
          data:
            notification_id: guardian_enrollment_write_failed
            title: 'Guardian: card did not save'
            message: >-
              Slot {{ target_slot | string | trim }} was written but reads back as
              {{ stored_back | length }} characters instead of 16. The helper
              input_text.rfid_{{ target_slot | string | trim }}_card_id almost certainly has its
              "max" set below 16, which truncates the card_id silently. The YAML
              helper in packages/guardian_rfid.yaml is already max: 16; if a
              leftover UI helper is still winning, delete it and restart.
        - action: script.guardian_notify_person
          continue_on_error: true
          data:
            slot: '{{ target_slot | string | trim }}'
            critical: true
            # An install fault, not a door event: the helper would not hold a
            # 16-character card_id. system, so it is not silenced by somebody
            # muting their own key.
            category: system
            severity: urgent
            title: 'Guardian: card did not save'
            message: >-
              Slot {{ target_slot | string | trim }} did not store a 16-character
              card_id. Check the max length of
              input_text.rfid_{{ target_slot | string | trim }}_card_id.
        - action: script.guardian_set_display
          data:
            value: DENIED_CARD
        - action: button.press
          target:
            entity_id: button.guardian_interior_portal_play_denied
        - action: script.turn_on
          target:
            entity_id: script.guardian_lamp_rejected
        - stop: Enrollment write did not survive; not reporting success.
      # Person name is optional. A non-empty pending name from the Guardian
      # panel (typed before the tap) is written here; an empty one leaves
      # whatever rfid_N_name already holds, so overwriting a slot without
      # typing a new name does not blank the previous person. Pending is
      # cleared only when there was nothing to write, or after the name write
      # reads back — a failed write must not throw away the typed name.
      - variables:
          pending_name: "{{ states('input_text.guardian_enroll_pending_name')
            | string | trim }}"
          pending_name_ok: "{{ pending_name not in ['', 'unknown', 'unavailable', 'none'] }}"
      - if:
        - condition: template
          value_template: '{{ pending_name_ok | bool }}'
        then:
        - action: input_text.set_value
          continue_on_error: true
          target:
            entity_id: input_text.rfid_{{ target_slot | string | trim }}_name
          data:
            value: '{{ pending_name }}'
        - variables:
            stored_name_back: "{{ states('input_text.rfid_' ~ (target_slot | string | trim)
              ~ '_name') | string | trim }}"
        - if:
          - condition: template
            value_template: '{{ stored_name_back == pending_name }}'
          then:
          - action: input_text.set_value
            continue_on_error: true
            target:
              entity_id: input_text.guardian_enroll_pending_name
            data:
              value: ''
          else:
          - action: persistent_notification.create
            data:
              notification_id: guardian_enrollment_name_failed
              title: 'Guardian: key name did not save'
              message: >-
                The card was enrolled in slot {{ target_slot | string | trim }},
                but the person name "{{ pending_name }}" did not stick on
                input_text.rfid_{{ target_slot | string | trim }}_name (reads
                back as "{{ stored_name_back }}"). The pending name was left
                in place — open Keys & PIN and Save on that key, or present
                the same card again during enrollment.
        else:
        - action: input_text.set_value
          continue_on_error: true
          target:
            entity_id: input_text.guardian_enroll_pending_name
          data:
            value: ''
      # The keypad choice is consumed by the card it selected, so the next card
      # goes back to first-free rather than silently overwriting the same slot.
      - action: input_text.set_value
        target:
          entity_id: input_text.guardian_enrollment_slot
        data:
          value: ''
      # Enrollment mode deliberately STAYS ON. It used to switch itself off after
      # one card, which made enrolling a set of cards a sequence of trips back to
      # the Home Assistant UI, and left no moment at which the portal could offer
      # a way out. The idle timer below is what bounds the session instead, and
      # the portal now shows "# to exit".
      - action: timer.start
        target:
          entity_id: timer.guardian_enrollment_window
      - event: guardian.card_enrolled
        event_data:
          slot: '{{ target_slot | string | trim }}'
          source: '{{ source }}'
          name: >-
            {% set from_pending = pending_name if pending_name_ok | bool else '' %}
            {% set raw = states('input_text.rfid_' ~ (target_slot | string | trim)
               ~ '_name') | string | trim %}
            {% set from_slot = raw if raw not in ['', 'unknown', 'unavailable'] else '' %}
            {{ from_slot if from_slot else from_pending }}
      - action: script.guardian_set_display
        data:
          value: GRANTED
      - action: button.press
        target:
          entity_id: button.guardian_interior_portal_play_welcome
      - action: script.turn_on
        target:
          entity_id: script.guardian_lamp_success
    default:
    - event: guardian.unknown_card_scanned
      event_data:
        source: '{{ source }}'
        result: '{{ scan_result }}'
        uid_bytes: '{{ uid_raw | length }}'
    # Reaching here with enrollment mode ON and no target slot means every slot is
    # occupied and nobody has picked one - that is the only remaining case, since
    # a malformed slot counts as empty. Switching enrollment off unconditionally
    # was worse than useless: a card that failed to match because its stored hash
    # was whitespace-padded or uppercase also landed here, and turning enrollment
    # off meant the obvious recovery - enable enrollment, tap the card again -
    # was cancelled by the very tap meant to fix it.
    #
    # The person holding the card is at the door, not at the Home Assistant web
    # UI, and the panel used to tell them "DENIED / Card not recognised" - which
    # is both wrong and unactionable. ENROLL_PICK says what is actually true and
    # what to press. The system will not choose a victim slot on its own.
    #
    # The notification below is always on, not gated by verbose notifications.
    # It prints live helper lengths next to the portal occupancy sensors so
    # "the screen says full" can be told from "the helpers are actually 64
    # characters" without a Developer Tools dump.
    - if:
      - condition: template
        value_template: '{{ enroll_mode | bool }}'
      then:
      - action: persistent_notification.create
        data:
          notification_id: guardian_enrollment_full
          title: 'Guardian: no free card slot'
          message: >-
            Enrollment mode is on, but process_rfid_scan found no writable
            slot. empty_slot='{{ empty_slot | trim }}'
            · target_slot='{{ target_slot | string | trim }}'
            · keypad='{{ states('input_text.guardian_enrollment_slot') }}'.

            Live helper lengths (occupied = 16 hex card_id after trim/lower):
            {% set ids = (states('sensor.guardian_rfid_slots') | string).split(',')
                         | map('trim') | reject('eq', '') | list %}{% for i in ids %}{{ i }}={{
              states('input_text.rfid_' ~ i ~ '_card_id') | string | trim | lower | length
            }}ch{% if not loop.last %}, {% endif %}{% endfor %}.

            Portal sensors (lag if they do not listen to the card_id helpers):
            free={{ states('sensor.guardian_rfid_free_slots') }},
            map={{ states('sensor.guardian_rfid_slot_map') }},
            target={{ states('sensor.guardian_enrollment_target_slot') }}.

            Press a slot digit on the portal keypad to overwrite a slot, or run
            script.guardian_clear_rfid_slot. Developer Tools -> States
            "Set State" does not persist and is not a clear. Enrollment mode
            has been left on.
      - action: script.guardian_set_display
        data:
          value: ENROLL_PICK
      - action: button.press
        target:
          entity_id: button.guardian_interior_portal_play_denied
      - action: timer.start
        target:
          entity_id: timer.guardian_enrollment_window
      - stop: All slots occupied; waiting for a keypad slot selection.
    # DENIED_CARD, not DENIED. They render differently on the portal: DENIED is
    # a PIN result and carries a "N PIN tries left" subtitle, which made a
    # rejected card report a password failure it had nothing to do with, using
    # a counter from an unrelated MFA session.
    - action: script.guardian_set_display
      data:
        value: DENIED_CARD
    - action: button.press
      target:
        entity_id: button.guardian_interior_portal_play_denied
    - action: script.turn_on
      target:
        entity_id: script.guardian_lamp_rejected
    # A rejected card used to produce nothing at all: no push, no persistent
    # notification, not even a data-log row - only a three-second flash on the
    # portal that nobody is necessarily standing in front of. That is why a
    # single mistyped stored hash could go undiagnosed indefinitely.
    - if:
      - condition: state
        entity_id: input_boolean.guardian_verbose_notifications
        state: 'on'
      then:
      - action: script.guardian_notify_broadcast
        continue_on_error: true
        data:
          category: security
          severity: important
          title: 'Guardian: card not recognised'
          message: >-
            An unrecognised card was presented at the {{ source }} reader.
            result={{ scan_result }} card_id_len={{ card_id_norm | length }}
            uid_bytes={{ (uid_raw | length + 1) // 3 if '-' in uid_raw else uid_raw | length }}.

guardian_reconcile_presence:
  alias: Guardian - Reconcile Presence
  description: >-
    Corrects a card's believed location from the reader it was just presented
    to. The doorbell reader is outside the door and the portal reader is inside
    it, so a scan is direct physical evidence of which side the card is on -
    evidence the system previously threw away, only ever updating presence after
    a scan AND a matching door opening.

    In a house with several resident cards someone forgets to scan regularly,
    and every missed scan used to strand that card on the wrong side
    permanently: a card left at "At home" also suppresses the Frigate
    person-detected-while-away alert, whose fallback gate is "all resident
    cards Away". Visitor keys are never occupants; this script will not set
    them At home, and will force Away if they somehow already are.

    Reconciling here, at scan time, rather than when a passage window expires is
    both simpler and strictly more correct - the card is provably at the
    reader's side BEFORE any crossing, so the rule is idempotent and holds
    whether or not a door opening follows.

    This runs before the MFA challenge is answered, so a scan alone moves
    presence without a PIN. That grants nothing: it never unlocks anything, a
    doorbell scan can only ever set "Away", and the only direction that sets
    "At home" - which is the one that could suppress the person-detected-while-
    away alert - requires physical access to the interior portal, i.e. already
    being inside, AND a resident policy. Cards marked Stolen/Lost are excluded
    by the caller. Visitor keys still authorize passage; they just never
    become occupants.
  mode: queued
  max: 10
  fields:
    slot:
      description: RFID slot id
      required: true
    source:
      description: doorbell or interior_portal
      required: true
  sequence:
  # VALIDATE THE SLOT BEFORE BUILDING ANY ENTITY ID OUT OF IT, and stop if it is
  # not on the rack. This ordering is the whole point of the block.
  #
  # slot_ok used to be computed in the SAME variables map as `current:
  # {{ states(entity) }}` and `expected:` — which reads
  # states('input_select.rfid_' ~ slot ~ '_policy') — so the validator ran after
  # both of the things it validates. Home Assistant renders a variables map as a
  # unit; there is no ordering to rely on and no way to short-circuit across
  # entries.
  #
  # With an empty or junk `slot` those two templates render
  # `input_select.rfid_` and `input_select.rfid__policy`. Neither is a valid
  # entity id — a trailing underscore, and a double underscore, both of which
  # Home Assistant's own valid_entity_id pattern rejects — so states() raises
  # TemplateError.
  #
  # And a raising template in a `variables:` block CANNOT BE GUARDED AT ALL.
  # continue_on_error does not apply to a render failure, and TemplateError is
  # one of the exceptions _handle_exception re-raises regardless. So the script
  # aborts, and because it is called blocking from process_rfid_scan the whole
  # scan is lost — the failure mode the fortieth and forty-second passes both
  # exist to prevent, reached through a door neither of them was looking at.
  #
  # Not reachable from process_rfid_scan today, which gates on its own slot_ok
  # first. It is reachable from Developer Tools and from any future caller, and
  # this script re-derives slot_ok precisely because it does not trust its
  # caller — so the validator has to actually run first.
  - variables:
      slot_id: '{{ slot | string | trim }}'
      slot_ok: "{{ (slot | string | trim) in ((states('sensor.guardian_rfid_slots')
        | string).split(',') | map('trim') | reject('eq', '') | list) }}"
  - condition: template
    value_template: "{{ slot_ok | bool and source in ['doorbell', 'interior_portal'] }}"
  # Everything below is now guaranteed a slot that is on the rack, so every
  # entity id built from it is a real one.
  - variables:
      entity: 'input_select.rfid_{{ slot_id }}'
      expected: "{{ 'Away' if (source == 'doorbell' or
        (states('input_select.rfid_' ~ slot_id ~ '_policy')
         | string | trim) == 'visitor') else 'At home' }}"
  - variables:
      current: '{{ states(entity) }}'
      # input_select.select_option RAISES on an option the helper does not have,
      # which would abort process_rfid_scan and lose the whole scan. Option
      # lists are declared in packages/guardian_rfid.yaml, but a leftover UI
      # helper from before the migration could still disagree. Check before
      # writing.
      option_exists: "{{ expected in (state_attr(entity, 'options')
        | default([], true) | list) }}"
  - condition: template
    value_template: "{{ current in ['At home', 'Away'] and
      current != expected and option_exists }}"
  - action: input_select.select_option
    target:
      entity_id: '{{ entity }}'
    data:
      option: '{{ expected }}'
  - event: guardian.presence_corrected
    event_data:
      slot: '{{ slot_id }}'
      name: >-
        {% set raw = states('input_text.rfid_' ~ slot_id ~ '_name')
           | string | trim %}
        {{ raw if raw not in ['', 'unknown', 'unavailable'] else 'Key ' ~ slot_id }}
      source: '{{ source }}'
      from: '{{ current }}'
      to: '{{ expected }}'
      timestamp: '{{ now().isoformat() }}'
  # Deliberately a persistent notification and not a push. Corrections are
  # routine housekeeping, not a security event, and pushing them would train the
  # family to ignore Guardian notifications.
  #
  # continue_on_error, and it is not cosmetic guarding for its own sake. This is
  # the LAST step of a script that process_rfid_scan calls with "action:", i.e.
  # blocking - so an error here does not stop here, it propagates into that
  # script and ends it, and the call site sits in front of the clone alarm and
  # the stolen-key alarm. That is the fortieth pass's bug exactly, one call deep,
  # and preflight could not see it: its raising-domain list is a list of DOMAINS,
  # and a step reading "action: script.guardian_reconcile_presence" matches none
  # of them. persistent_notification. is in that list; it just was not being
  # looked at from here. The forty-first pass teaches preflight to walk into
  # blocking script calls, which is what found this.
  - action: persistent_notification.create
    continue_on_error: true
    data:
      notification_id: 'guardian_presence_corrected_{{ slot_id }}'
      title: 'Guardian: presence corrected'
      message: >-
        {% set raw = states('input_text.rfid_' ~ slot_id ~ '_name')
           | string | trim %}
        {% set who = raw if raw not in ['', 'unknown', 'unavailable']
           else 'Card ' ~ slot_id %}
        {{ who }} was scanned at the
        {{ 'doorbell (outside)' if source == 'doorbell'
           else 'interior portal (inside)' }} reader while recorded as
        "{{ current }}". A scan was missed earlier; it is now "{{ expected }}".

guardian_authorize_passage:
  alias: Guardian - Authorize Passage
  description: >-
    Records intent; presence changes only after the reed switch proves the door
    opened.

    Each window holds a LIST of slots, so several people scanning within the
    same window are all completed by one door opening - previously each scan
    overwrote the last, and when three people left together and two scanned,
    only the last scanner's card flipped.

    The entry and exit windows are also independent now. Cancelling the opposite
    window on every scan meant that person A scanning at the doorbell to come in
    and person B scanning inside to go out seconds later destroyed A's window,
    so A's opening was reclassified by physics into a "keyed entry" push, an
    "unexplained door opening" push, or - in elevated mode - a siren.
  mode: queued
  max: 10
  fields:
    slot:
      required: true
    source:
      required: true
  sequence:
  - variables:
      slot_id: '{{ slot | string | trim }}'
  - condition: template
    value_template: "{{ (slot_id | string | trim) in ((states('sensor.guardian_rfid_slots')
      | string).split(',') | map('trim') | reject('eq', '') | list) }}"
  - choose:
    - conditions:
      - condition: template
        value_template: '{{ source == ''doorbell'' }}'
      sequence:
      - action: input_text.set_value
        target:
          entity_id: input_text.pending_entry_slot
        data:
          # The existing list is inherited ONLY while the timer is genuinely
          # running. If it expired, was cancelled, or was restored across a
          # restart, start a fresh list rather than trusting the input_text.
          #
          # The slot whitelist is sensor.guardian_rfid_slots. Nine ids join
          # to 17 characters; the helper's max is 32, so the write can never
          # be silently rejected.
          value: >-
            {%- set ids = (states('sensor.guardian_rfid_slots') | string).split(',')
                          | map('trim') | reject('eq', '') | list -%}
            {%- set active = is_state('timer.guardian_entry_window', 'active') -%}
            {%- set cur = (states('input_text.pending_entry_slot') | string)
                          if active else '' -%}
            {%- set have = cur.split(',') | map('trim')
                           | select('in', ids) | list -%}
            {{ ((have + [slot_id | string | trim]) | unique | list) | join(',') }}
      # timer.start on a running timer restarts the full 20s, so a late scanner
      # extends the window for everyone already queued. That is the right way
      # round for a group walking out together.
      - action: timer.start
        target:
          entity_id: timer.guardian_entry_window
      - action: input_text.set_value
        target:
          entity_id: input_text.last_doorbell_rfid_time
        data:
          value: '{{ now().isoformat() }}'
    - conditions:
      - condition: template
        value_template: '{{ source == ''interior_portal'' }}'
      sequence:
      - action: input_text.set_value
        target:
          entity_id: input_text.pending_exit_slot
        data:
          value: >-
            {%- set ids = (states('sensor.guardian_rfid_slots') | string).split(',')
                          | map('trim') | reject('eq', '') | list -%}
            {%- set active = is_state('timer.guardian_exit_window', 'active') -%}
            {%- set cur = (states('input_text.pending_exit_slot') | string)
                          if active else '' -%}
            {%- set have = cur.split(',') | map('trim')
                           | select('in', ids) | list -%}
            {{ ((have + [slot_id | string | trim]) | unique | list) | join(',') }}
      - action: timer.start
        target:
          entity_id: timer.guardian_exit_window
    default:
    - stop: Invalid RFID source; no passage window created.
      error: true
  - action: script.guardian_set_display
    data:
      value: GRANTED
  - action: button.press
    target:
      entity_id: button.guardian_interior_portal_play_welcome
  - action: script.turn_on
    target:
      entity_id: script.guardian_lamp_success
  
guardian_restore_lamp:
  alias: Guardian - Restore Lamp
  mode: parallel
  max: 10
  fields:
    was_on:
      required: true
    prev_brightness:
      required: false
    prev_rgb:
      required: false
    prev_kelvin:
      required: false
  sequence:
  - variables:
      # Challenge amber, alarm red, and success green are Guardian holds, never
      # a colour the camera lamp should be restored to. A restart or cloud lag
      # that snapshots the hold would otherwise paint it back as "previous".
      # Exact (255,150,0) misses Tapo HS round-trips (~255,149,0). Strings are
      # sequences in Jinja, so 'none' must not be treated as an RGB triple.
      # Always a valid entity id or the `none` sentinel - never the raw sensor
      # state. sensor.guardian_lamp_entity reads `unknown` on a half-copied
      # install and in the startup window, and `unknown` is not an entity id:
      # it fails the service schema with vol.Invalid, which is one of the
      # exceptions continue_on_error re-raises rather than swallows. Every
      # light.* step below that takes `lamp` as its target was therefore able
      # to end its whole sequence. `none` is ENTITY_MATCH_NONE - always valid,
      # matches nothing - and every consumer here already handles it.
      lamp: >-
        {% set e = states('sensor.guardian_lamp_entity') | string | trim %}
        {{ e if e is match('^(?!.+__)(?!_)[\da-z_]+(?<!_)\.(?!_)[\da-z_]+(?<!_)$') else 'none' }}
      rgb_hold: >-
        {%- set r = prev_rgb -%}
        {%- if r is none or (r | string | lower | trim) in
            ['none', 'unknown', 'unavailable', ''] -%}
          false
        {%- elif r is sequence and r is not string and r | count >= 3 -%}
          {%- set rv = r[0] | int(-1) -%}
          {%- set gv = r[1] | int(-1) -%}
          {%- set bv = r[2] | int(-1) -%}
          {{ (rv >= 240 and gv >= 100 and gv <= 180 and bv <= 40)
             or (rv >= 240 and gv <= 40 and bv <= 40)
             or (gv >= 240 and rv <= 40 and bv <= 40) }}
        {%- else -%}
          {%- set s = r | string | replace(' ', '') -%}
          {{ s in ['(255,150,0)', '[255,150,0]', '(255,0,0)', '[255,0,0]',
                   '(0,255,0)', '[0,255,0]'] }}
        {%- endif %}
  - choose:
    - conditions:
      - condition: template
        value_template: '{{ was_on | bool }}'
      sequence:
      - choose:
        - conditions:
          - condition: template
            value_template: '{{ prev_rgb is not none and prev_rgb | string not in
              [''None'', ''unknown'', ''unavailable'', ''none'']
              and not (rgb_hold | bool) }}'
          sequence:
          - action: light.turn_on
            target:
              entity_id: "{{ lamp }}"
            data:
              rgb_color: '{{ prev_rgb }}'
              brightness: '{{ prev_brightness | int(255) }}'
              transition: 0
        - conditions:
          - condition: template
            value_template: '{{ prev_kelvin is not none and prev_kelvin | int(0) >
              0 }}'
          sequence:
          - action: light.turn_on
            target:
              entity_id: "{{ lamp }}"
            data:
              color_temp_kelvin: '{{ prev_kelvin | int }}'
              brightness: '{{ prev_brightness | int(255) }}'
              transition: 0
        default:
        # Brightness-only while the Tapo is still in RGB hold (amber/red/green)
        # leaves that colour on. Drop the hold instead; callers sample if the
        # lamp should come back.
        - choose:
          - conditions:
            - condition: template
              value_template: '{{ rgb_hold | bool }}'
            sequence:
            - action: light.turn_off
              target:
                entity_id: "{{ lamp }}"
              data:
                transition: 0
          default:
          - action: light.turn_on
            target:
              entity_id: "{{ lamp }}"
            data:
              brightness: '{{ prev_brightness | int(255) }}'
              transition: 0
    default:
    - action: light.turn_off
      target:
        entity_id: "{{ lamp }}"
      data:
        transition: 0

guardian_lamp_feedback:
  alias: Guardian - Lamp Feedback Queue
  description: Serializes lamp flashes and restores the complete prior lamp state.
  mode: queued
  max: 10
  fields:
    result:
      required: true
  sequence:
  - variables:
      # Always a valid entity id or the `none` sentinel - never the raw sensor
      # state. sensor.guardian_lamp_entity reads `unknown` on a half-copied
      # install and in the startup window, and `unknown` is not an entity id:
      # it fails the service schema with vol.Invalid, which is one of the
      # exceptions continue_on_error re-raises rather than swallows. Every
      # light.* step below that takes `lamp` as its target was therefore able
      # to end its whole sequence. `none` is ENTITY_MATCH_NONE - always valid,
      # matches nothing - and every consumer here already handles it.
      lamp: >-
        {% set e = states('sensor.guardian_lamp_entity') | string | trim %}
        {{ e if e is match('^(?!.+__)(?!_)[\da-z_]+(?<!_)\.(?!_)[\da-z_]+(?<!_)$') else 'none' }}
  - wait_template: '{{ is_state(''input_boolean.guardian_lamp_sampling'', ''off'')
      }}'
    timeout: 00:00:15
    continue_on_timeout: true
  - condition: template
    value_template: '{{ lamp not in [''none'', '''', ''unknown'', ''unavailable'']
      and states(lamp) not in [''unknown'', ''unavailable'']
      }}'
  - variables:
      # Hold colours are never a restorable previous state. Green leftover is
      # a success flash; amber is the challenge; red is the alarm. Snapshotting
      # any of them and restoring it is how the Tapo stayed orange after the
      # opening had already been authenticated. Exact (255,150,0) misses the
      # Tapo HS round-trip; live checks also use color_mode + hue.
      hold: >-
        {%- set mode = state_attr(lamp, 'color_mode') | string | lower -%}
        {%- set rgb_mode = mode in ['hs', 'rgb', 'xy', 'unknown', 'none', ''] -%}
        {%- set r = state_attr(lamp, 'rgb_color') -%}
        {%- set hs = state_attr(lamp, 'hs_color') -%}
        {%- set rgb_ok = r is sequence and r is not string and r | count >= 3 -%}
        {%- set rv = r[0] | int(-1) if rgb_ok else -1 -%}
        {%- set gv = r[1] | int(-1) if rgb_ok else -1 -%}
        {%- set bv = r[2] | int(-1) if rgb_ok else -1 -%}
        {%- set rgb_hold = (rv >= 240 and gv >= 100 and gv <= 180 and bv <= 40)
            or (rv >= 240 and gv <= 40 and bv <= 40)
            or (gv >= 240 and rv <= 40 and bv <= 40) -%}
        {%- set hs_ok = hs is sequence and hs is not string and hs | count >= 2 -%}
        {%- set h = hs[0] | float(-1) if hs_ok else -1 -%}
        {%- set sat = hs[1] | float(-1) if hs_ok else -1 -%}
        {%- set hs_hold = sat >= 70 and ((h >= 25 and h <= 45)
            or (h <= 15 or h >= 345) or (h >= 100 and h <= 140)) -%}
        {{ rgb_mode and (rgb_hold or hs_hold) }}
  - variables:
      was_on: "{{ is_state(lamp, 'on') and not (hold | bool) }}"
      prev_brightness: '{{ state_attr(lamp, ''brightness'') | int(255)
        }}'
      prev_rgb: "{{ 'none' if hold | bool else state_attr(lamp, 'rgb_color') }}"
      prev_kelvin: '{{ state_attr(lamp, ''color_temp_kelvin'') }}'
  - choose:
    - conditions:
      - condition: template
        value_template: '{{ result == ''success'' }}'
      sequence:
      - action: light.turn_on
        target:
          entity_id: "{{ lamp }}"
        data:
          rgb_color:
          - 0
          - 255
          - 0
          brightness: 255
          transition: 0
      - delay: 00:00:01
    - conditions:
      - condition: template
        value_template: '{{ result == ''rejected'' }}'
      sequence:
      - repeat:
          count: 3
          sequence:
          - action: light.turn_on
            target:
              entity_id: "{{ lamp }}"
            data:
              rgb_color:
              - 255
              - 0
              - 0
              brightness: 255
              transition: 0
          - delay: '00:00:00.5'
          - action: light.turn_off
            target:
              entity_id: "{{ lamp }}"
            data:
              transition: 0
          - delay: '00:00:00.5'
  # A card-accepted flash during a live challenge is confirmation only. The
  # amber hold still belongs to the challenge; putting a snapshot back would
  # either re-paint orange as "previous" after auth, or steal the hold.
  - if:
    - condition: template
      value_template: "{{ is_state('input_text.portal_display_state', 'ALARM') }}"
    then:
    - stop: Alarm owns the lamp.
  - if:
    - condition: state
      entity_id: input_boolean.guardian_entry_challenge
      state: 'on'
    then:
    - action: light.turn_on
      target:
        entity_id: "{{ lamp }}"
      data:
        rgb_color:
        - 255
        - 150
        - 0
        brightness: 255
        transition: 0
    - stop: Challenge still holds the lamp amber.
  - action: script.guardian_restore_lamp
    data:
      was_on: '{{ was_on }}'
      prev_brightness: '{{ prev_brightness }}'
      prev_rgb: '{{ prev_rgb }}'
      prev_kelvin: '{{ prev_kelvin }}'
  # Tapo cloud lag can still report the hold colour after restore. Do not leave
  # it. Sampling is NOT started here: sample_ambient refuses to run while this
  # script is on. lamp_success samples after this returns.
  - if:
    - condition: template
      value_template: >-
        {% set mode = state_attr(lamp, 'color_mode') | string | lower %}
        {% set rgb_mode = mode in ['hs', 'rgb', 'xy', 'unknown', 'none', ''] %}
        {% set r = state_attr(lamp, 'rgb_color') %}
        {% set hs = state_attr(lamp, 'hs_color') %}
        {% set rgb_ok = r is sequence and r is not string and r | count >= 3 %}
        {% set rv = r[0] | int(-1) if rgb_ok else -1 %}
        {% set gv = r[1] | int(-1) if rgb_ok else -1 %}
        {% set bv = r[2] | int(-1) if rgb_ok else -1 %}
        {% set rgb_hold = (rv >= 240 and gv >= 100 and gv <= 180 and bv <= 40)
            or (rv >= 240 and gv <= 40 and bv <= 40)
            or (gv >= 240 and rv <= 40 and bv <= 40) %}
        {% set hs_ok = hs is sequence and hs is not string and hs | count >= 2 %}
        {% set h = hs[0] | float(-1) if hs_ok else -1 %}
        {% set sat = hs[1] | float(-1) if hs_ok else -1 %}
        {% set hs_hold = sat >= 70 and ((h >= 25 and h <= 45)
            or (h <= 15 or h >= 345) or (h >= 100 and h <= 140)) %}
        {{ is_state(lamp, 'on') and rgb_mode and (rgb_hold or hs_hold) }}
    then:
    - action: light.turn_off
      target:
        entity_id: "{{ lamp }}"

guardian_lamp_success:
  alias: Guardian Lamp Success
  mode: queued
  sequence:
  - variables:
      # Always a valid entity id or the `none` sentinel - never the raw sensor
      # state. sensor.guardian_lamp_entity reads `unknown` on a half-copied
      # install and in the startup window, and `unknown` is not an entity id:
      # it fails the service schema with vol.Invalid, which is one of the
      # exceptions continue_on_error re-raises rather than swallows. Every
      # light.* step below that takes `lamp` as its target was therefore able
      # to end its whole sequence. `none` is ENTITY_MATCH_NONE - always valid,
      # matches nothing - and every consumer here already handles it.
      lamp: >-
        {% set e = states('sensor.guardian_lamp_entity') | string | trim %}
        {{ e if e is match('^(?!.+__)(?!_)[\da-z_]+(?<!_)\.(?!_)[\da-z_]+(?<!_)$') else 'none' }}
  - action: script.guardian_lamp_feedback
    data:
      result: success
  - condition: template
    value_template: "{{ not is_state('input_text.portal_display_state', 'ALARM')
      and not is_state('input_boolean.guardian_entry_challenge', 'on') }}"
  - variables:
      leftover_hold: >-
        {%- set mode = state_attr(lamp, 'color_mode') | string | lower -%}
        {%- set rgb_mode = mode in ['hs', 'rgb', 'xy', 'unknown', 'none', ''] -%}
        {%- set r = state_attr(lamp, 'rgb_color') -%}
        {%- set hs = state_attr(lamp, 'hs_color') -%}
        {%- set rgb_ok = r is sequence and r is not string and r | count >= 3 -%}
        {%- set rv = r[0] | int(-1) if rgb_ok else -1 -%}
        {%- set gv = r[1] | int(-1) if rgb_ok else -1 -%}
        {%- set bv = r[2] | int(-1) if rgb_ok else -1 -%}
        {%- set rgb_hold = (rv >= 240 and gv >= 100 and gv <= 180 and bv <= 40)
            or (rv >= 240 and gv <= 40 and bv <= 40)
            or (gv >= 240 and rv <= 40 and bv <= 40) -%}
        {%- set hs_ok = hs is sequence and hs is not string and hs | count >= 2 -%}
        {%- set h = hs[0] | float(-1) if hs_ok else -1 -%}
        {%- set sat = hs[1] | float(-1) if hs_ok else -1 -%}
        {%- set hs_hold = sat >= 70 and ((h >= 25 and h <= 45)
            or (h <= 15 or h >= 345) or (h >= 100 and h <= 140)) -%}
        {{ is_state(lamp, 'on') and rgb_mode and (rgb_hold or hs_hold) }}
  - choose:
    - conditions:
      - condition: template
        value_template: '{{ leftover_hold | bool }}'
      sequence:
      - action: light.turn_off
        target:
          entity_id: "{{ lamp }}"
      - action: script.guardian_sample_ambient_light
    - conditions:
      - condition: template
        value_template: "{{ is_state(lamp, 'off') }}"
      sequence:
      - action: script.guardian_sample_ambient_light

guardian_lamp_rejected:
  alias: Guardian Lamp Rejected
  mode: queued
  sequence:
  - action: script.guardian_lamp_feedback
    data:
      result: rejected

guardian_lamp_warning:
  alias: Guardian Lamp Warning
  description: >-
    Holds the lamp amber for the duration of an entry challenge, then puts it
    back exactly as it was.

    Deliberately NOT routed through guardian_lamp_feedback: that queue exists to
    serialise short flashes and restores immediately afterwards, whereas this has
    to HOLD for as long as the challenge runs so someone walking in at night can
    see that the system is waiting on them.
  # restart, so a second opening inside one challenge re-arms the hold against
  # the state captured by the first run rather than stacking two restores.
  mode: restart
  sequence:
  - variables:
      # Always a valid entity id or the `none` sentinel - never the raw sensor
      # state. sensor.guardian_lamp_entity reads `unknown` on a half-copied
      # install and in the startup window, and `unknown` is not an entity id:
      # it fails the service schema with vol.Invalid, which is one of the
      # exceptions continue_on_error re-raises rather than swallows. Every
      # light.* step below that takes `lamp` as its target was therefore able
      # to end its whole sequence. `none` is ENTITY_MATCH_NONE - always valid,
      # matches nothing - and every consumer here already handles it.
      lamp: >-
        {% set e = states('sensor.guardian_lamp_entity') | string | trim %}
        {{ e if e is match('^(?!.+__)(?!_)[\da-z_]+(?<!_)\.(?!_)[\da-z_]+(?<!_)$') else 'none' }}
  - condition: template
    value_template: "{{ lamp not in ['none', 'unknown', 'unavailable', '']
      and states(lamp) not in ['unknown', 'unavailable'] }}"
  - variables:
      # A leftover challenge hold is on + near-amber (Tapo reports HS-rounded
      # RGB, not exact 255,150,0). Restoring that snapshot (mode: restart
      # re-reads live attrs) leaves the Tapo stuck amber after the challenge
      # ends. Do not hand that rgb to restore, and do not treat a hold as
      # was_on: brightness-only restore would leave the colour on.
      hold: >-
        {%- set mode = state_attr(lamp, 'color_mode') | string | lower -%}
        {%- set rgb_mode = mode in ['hs', 'rgb', 'xy', 'unknown', 'none', ''] -%}
        {%- set r = state_attr(lamp, 'rgb_color') -%}
        {%- set hs = state_attr(lamp, 'hs_color') -%}
        {%- set rgb_ok = r is sequence and r is not string and r | count >= 3 -%}
        {%- set rv = r[0] | int(-1) if rgb_ok else -1 -%}
        {%- set gv = r[1] | int(-1) if rgb_ok else -1 -%}
        {%- set bv = r[2] | int(-1) if rgb_ok else -1 -%}
        {%- set rgb_hold = (rv >= 240 and gv >= 100 and gv <= 180 and bv <= 40)
            or (rv >= 240 and gv <= 40 and bv <= 40)
            or (gv >= 240 and rv <= 40 and bv <= 40) -%}
        {%- set hs_ok = hs is sequence and hs is not string and hs | count >= 2 -%}
        {%- set h = hs[0] | float(-1) if hs_ok else -1 -%}
        {%- set sat = hs[1] | float(-1) if hs_ok else -1 -%}
        {%- set hs_hold = sat >= 70 and ((h >= 25 and h <= 45)
            or (h <= 15 or h >= 345) or (h >= 100 and h <= 140)) -%}
        {{ rgb_mode and (rgb_hold or hs_hold) }}
  - variables:
      was_on: "{{ is_state(lamp, 'on') and not (hold | bool) }}"
      prev_brightness: "{{ state_attr(lamp, 'brightness') | int(255) }}"
      prev_rgb: "{{ 'none' if hold | bool else state_attr(lamp, 'rgb_color') }}"
      prev_kelvin: "{{ state_attr(lamp, 'color_temp_kelvin') }}"
  - action: light.turn_on
    target:
      entity_id: "{{ lamp }}"
    data:
      rgb_color:
      - 255
      - 150
      - 0
      brightness: 255
      transition: 0
  # The timeout is a backstop only. Every path that ends a challenge clears the
  # boolean, but a restart mid-challenge would otherwise strand the lamp amber
  # forever, which is the same class of bug as the stranded blacked-out lamp
  # that guardian_lamp_presample exists to fix.
  - wait_template: "{{ is_state('input_boolean.guardian_entry_challenge', 'off') }}"
    timeout: 00:05:00
    continue_on_timeout: true
  # A challenge that ended by TIMING OUT raises a major alarm, and the alarm
  # handler owns the lamp from that moment - it is holding it full red. Restoring
  # here would quietly undo the most visible part of an active alarm.
  - condition: template
    value_template: "{{ not is_state('input_text.portal_display_state', 'ALARM') }}"
  - action: script.guardian_restore_lamp
    data:
      was_on: '{{ was_on }}'
      prev_brightness: '{{ prev_brightness }}'
      prev_rgb: '{{ prev_rgb }}'
      prev_kelvin: '{{ prev_kelvin }}'
  - if:
    - condition: template
      value_template: >-
        {% set mode = state_attr(lamp, 'color_mode') | string | lower %}
        {% set rgb_mode = mode in ['hs', 'rgb', 'xy', 'unknown', 'none', ''] %}
        {% set r = state_attr(lamp, 'rgb_color') %}
        {% set hs = state_attr(lamp, 'hs_color') %}
        {% set rgb_ok = r is sequence and r is not string and r | count >= 3 %}
        {% set rv = r[0] | int(-1) if rgb_ok else -1 %}
        {% set gv = r[1] | int(-1) if rgb_ok else -1 %}
        {% set bv = r[2] | int(-1) if rgb_ok else -1 %}
        {% set rgb_hold = (rv >= 240 and gv >= 100 and gv <= 180 and bv <= 40)
            or (rv >= 240 and gv <= 40 and bv <= 40)
            or (gv >= 240 and rv <= 40 and bv <= 40) %}
        {% set hs_ok = hs is sequence and hs is not string and hs | count >= 2 %}
        {% set h = hs[0] | float(-1) if hs_ok else -1 %}
        {% set sat = hs[1] | float(-1) if hs_ok else -1 %}
        {% set hs_hold = sat >= 70 and ((h >= 25 and h <= 45)
            or (h <= 15 or h >= 345) or (h >= 100 and h <= 140)) %}
        {{ is_state(lamp, 'on') and rgb_mode and (rgb_hold or hs_hold) }}
    then:
    - action: light.turn_off
      target:
        entity_id: "{{ lamp }}"
    - action: script.guardian_sample_ambient_light

# Keep this key line. It was deleted once (commit 903d1fd) by a hunk that
# appended the amber cleanup above, which spliced this whole script into
# guardian_lamp_warning as duplicate alias/description/mode/sequence keys.
# Home Assistant takes the LAST of a duplicate key, so guardian_lamp_warning
# silently became this script: the Elevated Opening Supervisor's
# "script.turn_on: guardian_lamp_warning" cancelled the challenge it had just
# opened, and every unauthorised elevated opening went completely unanswered -
# no countdown, no amber, no chirp, no alarm. See the parse check in DEPLOY.md.
guardian_clear_entry_challenge:
  alias: Guardian - Clear Entry Challenge
  description: >-
    Ends a grace challenge successfully after BOTH factors (registered card
    and master PIN) have been presented. Callers must have already set
    guardian_challenge_card_ok and guardian_challenge_pin_ok; this script
    does not re-check them, it is the shared completion path.

    It also clears any PIN challenge that happened to be open, because the
    opening it was guarding has now been accounted for; leaving one running would
    let its own 40s timeout fire a major alarm for an entry that was already
    authenticated.
  mode: queued
  max: 3
  fields:
    method:
      description: card or pin
      required: false
    detail:
      description: Free text for the confirmation push
      required: false
    slot:
      description: RFID slot id when the challenge was answered with a card
      required: false
      example: '1'
  sequence:
  - variables:
      origin: "{{ states('input_text.guardian_challenge_origin') | string | trim }}"
  # Stop the amber hold BEFORE clearing the challenge flag. The warning script
  # waits on that flag; turning the flag off first lets it restore a near-amber
  # snapshot after auth has already cleaned up. script.turn_off aborts the wait
  # without running restore. Timeout/alarm does not call this script, so that
  # path still wakes on the flag and sees ALARM.
  - action: script.turn_off
    target:
      entity_id: script.guardian_lamp_warning
  - action: timer.cancel
    target:
      entity_id:
      - timer.guardian_entry_challenge
      - timer.guardian_mfa_window
  - action: input_boolean.turn_off
    target:
      entity_id:
      - input_boolean.guardian_entry_challenge
      - input_boolean.portal_mfa_pending
      - input_boolean.guardian_challenge_card_ok
      - input_boolean.guardian_challenge_pin_ok
  - action: input_number.set_value
    target:
      entity_id: input_number.mfa_failed_attempts
    data:
      value: 0
  - action: input_text.set_value
    target:
      entity_id:
      - input_text.guardian_challenge_origin
      - input_text.pending_mfa_slot
      - input_text.pending_mfa_source
    data:
      value: none
  - event: guardian.entry_challenge_cleared
    event_data:
      method: "{{ method | default('unknown', true) }}"
      origin: '{{ origin }}'
      detail: "{{ detail | default('', true) }}"
      timestamp: '{{ now().isoformat() }}'
  # Informational, not high priority. An answered challenge is the system working
  # as designed; only an unanswered one is an alarm. Card answers go to that
  # person; PIN answers have no slot and broadcast.
  - if:
    - condition: template
      value_template: >-
        {{ (slot | default('', true) | string | trim) in
           ((states('sensor.guardian_rfid_slots') | string).split(',')
            | map('trim') | reject('eq', '') | list) }}
    then:
    - action: script.guardian_notify_person
      continue_on_error: true
      data:
        slot: '{{ slot | string | trim }}'
        critical: false
        category: mine
        severity: important
        title: 'Guardian: entry authenticated'
        message: >-
          An elevated-mode opening from {{ origin if origin not in
          ['none', 'unknown', ''] else 'an unknown direction' }} was authenticated
          by {{ method | default('an unknown method', true) }}{{
          ' (' ~ detail ~ ')' if detail | default('', true) | length > 0 else '' }}.
    else:
    - action: script.guardian_notify_broadcast
      continue_on_error: true
      data:
        category: security
        severity: important
        title: 'Guardian: entry authenticated'
        message: >-
          An elevated-mode opening from {{ origin if origin not in
          ['none', 'unknown', ''] else 'an unknown direction' }} was authenticated
          by {{ method | default('an unknown method', true) }}{{
          ' (' ~ detail ~ ')' if detail | default('', true) | length > 0 else '' }}.

guardian_doorbell_exit_pin_prompt:
  alias: Guardian - Doorbell Exit PIN Prompt
  description: >-
    Sends the owner-only textInput PIN prompt for the doorbell-exit window.
    critical is false so an unmapped slot NEVER fans the PIN field out through
    broadcast. The reminder automation and the start script both call this;
    the Companion tag replaces the previous shade notification rather than
    stacking copies.
  mode: queued
  max: 5
  fields:
    slot:
      description: RFID slot that scanned at the doorbell
      required: true
      example: '1'
  sequence:
  - variables:
      which: '{{ slot | string | trim }}'
      who: >-
        {% set raw = states('input_text.rfid_' ~ (slot | string | trim) ~ '_name')
                     | string | trim %}
        {{ raw if raw not in ['', 'unknown', 'unavailable', 'none']
           else ('Key ' ~ (slot | string | trim)) }}
      minutes: "{{ states('input_number.guardian_doorbell_exit_pin_minutes') | int(10) }}"
      mapped: "{{ (slot | string | trim) in ((states('sensor.guardian_rfid_slots')
        | string).split(',') | map('trim') | reject('eq', '') | list)
        and (states('input_select.rfid_' ~ (slot | string | trim) ~ '_notify_target')
             | string | trim) not in ['none', '', 'unknown', 'unavailable']
        and (states('input_select.rfid_' ~ (slot | string | trim) ~ '_notify_target')
             | string | trim) in ((states('sensor.guardian_notify_targets_available')
             | string).split(',') | map('trim') | reject('eq', '') | list) }}"
  # Guarded: the push below is not a notice about the exit window, it IS the
  # window - the PIN field that lets this person back in without an alarm. This
  # badge is the fallback for someone already at a browser, and it must not be
  # able to cancel the thing it is a fallback for.
  - action: persistent_notification.create
    continue_on_error: true
    data:
      notification_id: guardian_doorbell_exit_pin
      title: 'Guardian: confirm exit PIN'
      message: >-
        {{ who }} scanned at the doorbell. Enter the master PIN from the
        linked phone within {{ minutes }} minutes, or at the interior keypad
        if you can reach it. An unanswered window becomes a full alarm.
  # companion: doorbell_exit_pin, not nested data:. A script field named
  # data is stringified on the way in, extra is mapping is then false, and
  # notify.send_message drops the PIN field. guardian_notify_person builds
  # the YAML-literal Companion payload itself.
  - action: script.guardian_notify_person
    data:
      slot: '{{ which }}'
      critical: false
      # This one is not a notice, it is the interaction: the PIN field that
      # lets this person out. urgent so it survives every level, and mine
      # because it is addressed to them by name.
      category: mine
      severity: urgent
      companion: doorbell_exit_pin
      title: 'Guardian: confirm your exit'
      message: >-
        Your card was scanned at the doorbell. Super surveillance is on and
        that reader has no keypad, so the master PIN is required from this
        phone within {{ minutes }} minutes. Tap Enter PIN, type it, and send,
        or open Guardian and type it there. An unanswered prompt becomes a
        full alarm.
    response_variable: prompt_result
  - if:
    - condition: template
      value_template: '{{ not (mapped | bool) }}'
    then:
    # Prompt itself must not leave the owner's phone. This household warning
    # has no textInput, so someone else can still act (keypad, or linking a
    # phone) before the 10 minutes become a false alarm.
    - action: script.guardian_notify_broadcast
      continue_on_error: true
      data:
        category: security
        severity: important
        title: 'Guardian: doorbell exit needs a phone'
        message: >-
          {{ who }} scanned at the doorbell while elevated mode was on, but
          that key has no linked phone, so the PIN prompt could not be
          delivered. Enter the master PIN at the interior keypad within
          {{ minutes }} minutes or a full alarm will sound. Link a phone on
          Keys, People & Alerts.

guardian_start_doorbell_exit_pin:
  alias: Guardian - Start Doorbell Exit PIN Window
  description: >-
    Opens the 10-minute phone-PIN window after an elevated doorbell-exit scan.
    If a 30s keypad challenge is running it is converted (one clock only) -
    never via guardian_clear_entry_challenge, which would report the opening
    as authenticated. A second scan while the window is already open updates
    the slot and resends the prompt but does not restart the timer.
  mode: queued
  max: 5
  fields:
    slot:
      required: true
    convert_challenge:
      required: false
      default: false
  sequence:
  - variables:
      which: '{{ slot | string | trim }}'
      converting: "{{ convert_challenge | default(false, true) | string | trim | lower
        in ['true', 'on', 'yes', '1'] }}"
      already: "{{ is_state('input_boolean.guardian_doorbell_exit_pin', 'on') }}"
  - if:
    - condition: template
      value_template: '{{ converting | bool }}'
    then:
    - action: timer.cancel
      target:
        entity_id: timer.guardian_entry_challenge
    - action: input_boolean.turn_off
      target:
        entity_id:
        - input_boolean.guardian_entry_challenge
        - input_boolean.guardian_challenge_card_ok
        - input_boolean.guardian_challenge_pin_ok
        - input_boolean.portal_mfa_pending
    - action: timer.cancel
      target:
        entity_id: timer.guardian_mfa_window
    - action: input_text.set_value
      target:
        entity_id: input_text.guardian_challenge_origin
      data:
        value: none
  - action: input_text.set_value
    target:
      entity_id: input_text.guardian_doorbell_exit_slot
    data:
      value: '{{ which }}'
  - if:
    - condition: template
      value_template: '{{ already | bool }}'
    then:
    - action: script.guardian_doorbell_exit_pin_prompt
      data:
        slot: '{{ which }}'
    - stop: Window already open; prompt resent without restarting the clock.
  - action: input_boolean.turn_on
    target:
      entity_id: input_boolean.guardian_doorbell_exit_pin
  - action: input_number.set_value
    target:
      entity_id: input_number.mfa_failed_attempts
    data:
      value: 0
  - action: timer.start
    target:
      entity_id: timer.guardian_doorbell_exit_pin_window
    data:
      duration: >-
        {% set m = states('input_number.guardian_doorbell_exit_pin_minutes') | int(10) %}
        {{ '00:%02d:00' % (m if m < 60 else 59) }}
  - event: guardian.doorbell_exit_pin_started
    event_data:
      slot: '{{ which }}'
      minutes: "{{ states('input_number.guardian_doorbell_exit_pin_minutes') | int(10) }}"
      timestamp: '{{ now().isoformat() }}'
  - action: script.turn_on
    target:
      entity_id: script.guardian_lamp_success
  - action: button.press
    target:
      entity_id: button.guardian_interior_portal_play_mfa_challenge
    continue_on_error: true
  - action: script.guardian_set_display
    data:
      value: MFA
  - action: script.guardian_doorbell_exit_pin_prompt
    data:
      slot: '{{ which }}'

guardian_clear_doorbell_exit_pin:
  alias: Guardian - Clear Doorbell Exit PIN Window
  description: >-
    Ends the doorbell-exit phone-PIN window successfully. Callers have already
    confirmed the PIN via script.guardian_pin_matches. Does not authorize an
    entry passage window - the person is already outside.
  mode: queued
  max: 3
  fields:
    method:
      description: phone or keypad
      required: false
    slot:
      required: false
  sequence:
  - variables:
      which: >-
        {% set s = slot | default('', true) | string | trim %}
        {% set ids = (states('sensor.guardian_rfid_slots') | string).split(',')
                     | map('trim') | reject('eq', '') | list %}
        {{ s if s in ids else (states('input_text.guardian_doorbell_exit_slot')
           | string | trim) }}
  - action: timer.cancel
    target:
      entity_id: timer.guardian_doorbell_exit_pin_window
  - action: input_boolean.turn_off
    target:
      entity_id: input_boolean.guardian_doorbell_exit_pin
  - action: input_number.set_value
    target:
      entity_id: input_number.mfa_failed_attempts
    data:
      value: 0
  - action: input_text.set_value
    target:
      entity_id: input_text.guardian_doorbell_exit_slot
    data:
      value: none
  - action: persistent_notification.dismiss
    continue_on_error: true
    data:
      notification_id: guardian_doorbell_exit_pin
  - event: guardian.doorbell_exit_pin_cleared
    event_data:
      method: "{{ method | default('unknown', true) }}"
      slot: '{{ which }}'
      timestamp: '{{ now().isoformat() }}'
  - if:
    - condition: template
      value_template: "{{ states('input_text.portal_display_state') not in
        ['ALARM', 'IDLE'] }}"
    then:
    - action: script.guardian_set_display
      data:
        value: IDLE
  - action: script.turn_on
    target:
      entity_id: script.guardian_lamp_success
  - if:
    - condition: template
      value_template: >-
        {{ (which | string | trim) in
           ((states('sensor.guardian_rfid_slots') | string).split(',')
            | map('trim') | reject('eq', '') | list) }}
    then:
    - action: script.guardian_notify_person
      continue_on_error: true
      data:
        slot: '{{ which }}'
        critical: false
        # Replaces the tagged PIN shade on the same phone. urgent for the same
        # reason the prompt is: a level that suppressed this would leave a
        # dead PIN field sitting on the lock screen with nothing to clear it.
        category: mine
        severity: urgent
        companion: doorbell_exit_done
        title: 'Guardian: exit confirmed'
        message: >-
          The doorbell-exit PIN was accepted
          ({{ method | default('unknown', true) }}). No alarm.

guardian_apply_doorbell_exit_pin:
  alias: Guardian - Apply Doorbell Exit PIN
  description: >-
    Shared success/fail path for the doorbell-exit window. Callers pass the
    typed PIN; compare is script.guardian_pin_matches only. Used by the
    Companion reply automation and by the Guardian panel. Refuses unless the
    window is open. Never stores the PIN.
  mode: queued
  max: 10
  fields:
    pin:
      description: The typed master PIN
      required: true
      selector:
        text:
          type: password
    method:
      description: phone or panel
      required: false
      default: phone
  sequence:
  - condition: state
    entity_id: input_boolean.guardian_doorbell_exit_pin
    state: 'on'
  - action: script.guardian_pin_matches
    data:
      pin: '{{ pin }}'
    response_variable: pin_check
  - choose:
    - conditions:
      - condition: template
        value_template: '{{ pin_check.matches | bool }}'
      sequence:
      - action: script.guardian_clear_doorbell_exit_pin
        data:
          method: "{{ method | default('phone', true) }}"
          slot: "{{ states('input_text.guardian_doorbell_exit_slot') }}"
      - variables:
          result:
            outcome: accepted
            matches: true
      - stop: PIN accepted
        response_variable: result
    default:
    - action: input_number.set_value
      target:
        entity_id: input_number.mfa_failed_attempts
      data:
        value: "{{ states('input_number.mfa_failed_attempts') | int(0) + 1 }}"
    - choose:
      - conditions:
        - condition: template
          value_template: "{{ states('input_number.mfa_failed_attempts') | int(0)
            >= 3 }}"
        sequence:
        - action: input_number.set_value
          target:
            entity_id: input_number.mfa_failed_attempts
          data:
            value: 0
        - action: timer.cancel
          target:
            entity_id: timer.guardian_doorbell_exit_pin_window
        - action: input_boolean.turn_off
          target:
            entity_id: input_boolean.guardian_doorbell_exit_pin
        - action: input_text.set_value
          target:
            entity_id: input_text.guardian_doorbell_exit_slot
          data:
            value: none
        - action: persistent_notification.dismiss
          continue_on_error: true
          data:
            notification_id: guardian_doorbell_exit_pin
        - event: guardian.major_alarm
          event_data:
            reason: Maximum PIN attempts exceeded (doorbell-exit PIN)
        - variables:
            result:
              outcome: lockout
              matches: false
        - stop: PIN lockout
          response_variable: result
      default:
      - action: script.guardian_doorbell_exit_pin_prompt
        continue_on_error: true
        data:
          slot: "{{ states('input_text.guardian_doorbell_exit_slot') }}"
      - variables:
          result:
            outcome: rejected
            matches: false
            attempts_left: "{{ [0, 3 - (states('input_number.mfa_failed_attempts')
              | int(0))] | max }}"
      - stop: PIN rejected
        response_variable: result
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
